Leandrodn/Project5-6-RDM-RegistatiePaal/Onderzoek/Gebruikers_Onderzoek/Enquete_Document.pdf

# Enquête

# Werkplaatsregistratie

Wie: 2e Jaars Technische Informatica studenten

Waarom: Uitzoeken wat studenten het fijnste registratiesysteem vinden

Doel: Automatiseren van registratie studenten die de werkplaatsen gebruiken

Waarvoor: Project – Help de RDM werkplaatsen met studentenregistratie

# Graag Scannen en Invullen

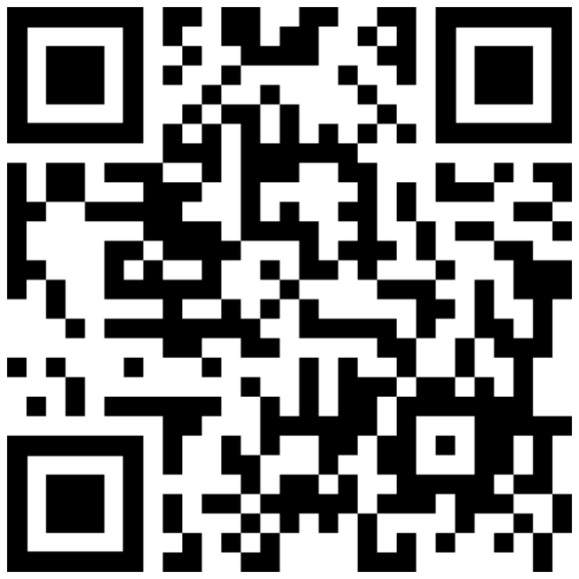
[picture p20: figure]
