Leandrodn/Project5-6-RDM-RegistatiePaal/Onderzoek/Gebruikers_Onderzoek/Onderzoek_Registratiemethodes.pdf

# Onderzoek Registratiemethodes – Project

56

Help de RDM-werkplaatsen om beter grip te krijgen op het gebruik van de werkplaatsen!


Projectleden:
- Matthijs Briel (0988991)
- Leandro de Nijs (1003440)
- Tom van Pelt (1003212)
- Gijs Kortlever (1003152)
Inleverdatum: 6 Februari 2022
Begeleiders: Erwin de Mos & S.M. Hekkelman Bedrijfsbegeleider (Product Owner): F.W.J. Joosten Gladon Gelegenheid: Eerste Kans


# Inhoudsopgave

# Inleiding

In dit document wordt er onderzocht wat de beste registratiemethode is voor het gebruik maken van de werkplaatsen. Hiervoor wordt er een enquête gedaan onder de studenten die gebruik maken van de werkplaatsen en worden er interviews gedaan met een aantal instructeurs om een beeld te krijgen wat zij voor ogen hebben en of zij nog speciale wensen / eisen hebben voor hun werkplaats.

De mensen die gebruik gaan maken van ons registratiesysteem zijn de studenten die een werkplaats willen gebruiken. De instructeurs worden hierdoor ondersteund door een taak van hun erg te verlichten (het handmatig registreren van studenten).

# Enquête Onder Studenten

Onder de studenten wordt er dus een enquête gehouden. Via een enquête kunnen we heel makkelijk een grootte doelgroep bereiken. De minimale hoeveelheid studenten die aan onze enquête moet deelnemen valt te bepalen met een berekening. Om dit te berekenen hebben we een aantal initiële waardes nodig.

- De populatie: dit is aan hoeveel mensen de enquête wordt voorgelegd. Dit hangt ook af van hoelang we de data willen ontvangen, we laten de enquête een week hangen in de drie meest gebruikte werkplaatsen, de houtwerkplaats, metaalwerkplaats en het Protolab. Ook zullen er een of meerdere dagen actief mensen werven voor deelname. Om onze populatie dus te bepalen moeten we weten hoeveel mensen er in een week tijd naar de werkplaatsen gaan, dit kunnen we halen uit de data van 2019 die we hebben gekregen van ons product owner. Gemiddeld komen er 172 studenten per week naar de werkplaatsen, dit verdelen over 8 werkplaatsen is 21 studenten per week per werkplaats. De enquête wordt gehouden bij drie werkplaatsen, dus 21 x 3 = 63 studenten.
- Foutmarge: die is hoe zeker wij ervan zijn dat de mening van de ondervraagde overeenkomt met die van de totale populatie. Voor enquêtes wordt vaak een foutmarge genomen van 5%, er zal hier ook mee werken.
- Betrouwbaarheidsinterval: dit is hoe zeker wij zijn dat het resultaat een nauwkeurige afspiegeling van de populatie vormt. Voor enquêtes wordt vaak het 95% betrouwbaarheid interval gebruikt, er zal hier ook mee gerekend worden.
- Als we dit berekenen via een formule of via een online calculator, komen we erachter dat we minimaal 55 respondenten moeten verkrijgen voor een betrouwbaar resultaat. Zie Figuur 1.

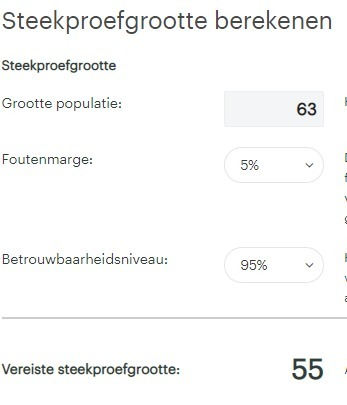
[picture p21: figure]

Figuur 1 - Steekproefgrootte Berekening

1

1 Steekproefomvang berekening: https://nl.checkmarket.com/steekproefcalculator/

### Link naar enquête

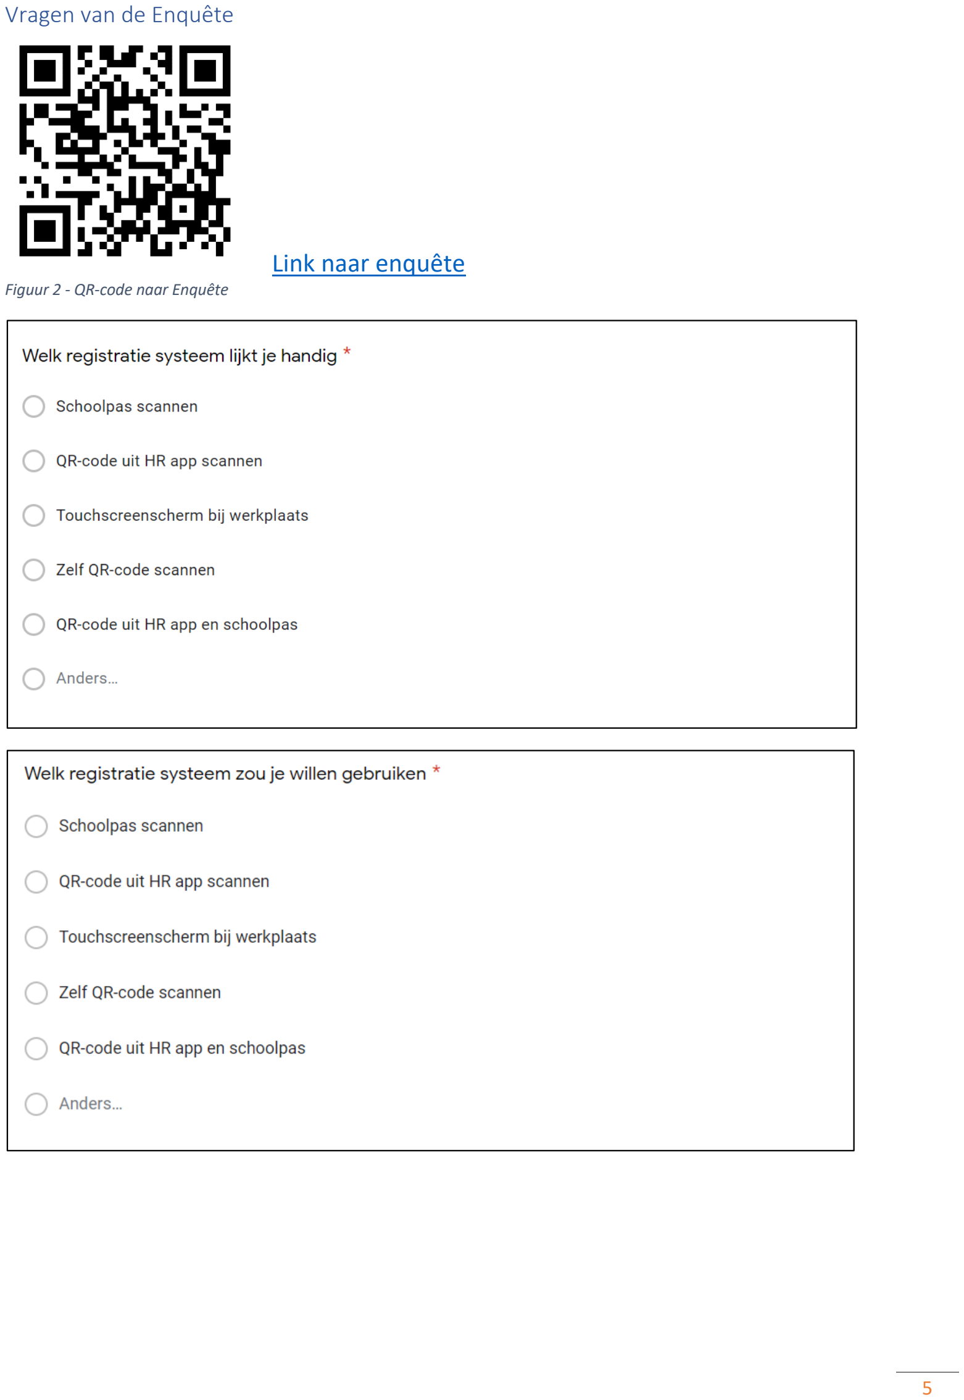
[picture p22: page 5]

### Vragen van de Enquête

Figuur 2 - QR-code naar Enquête

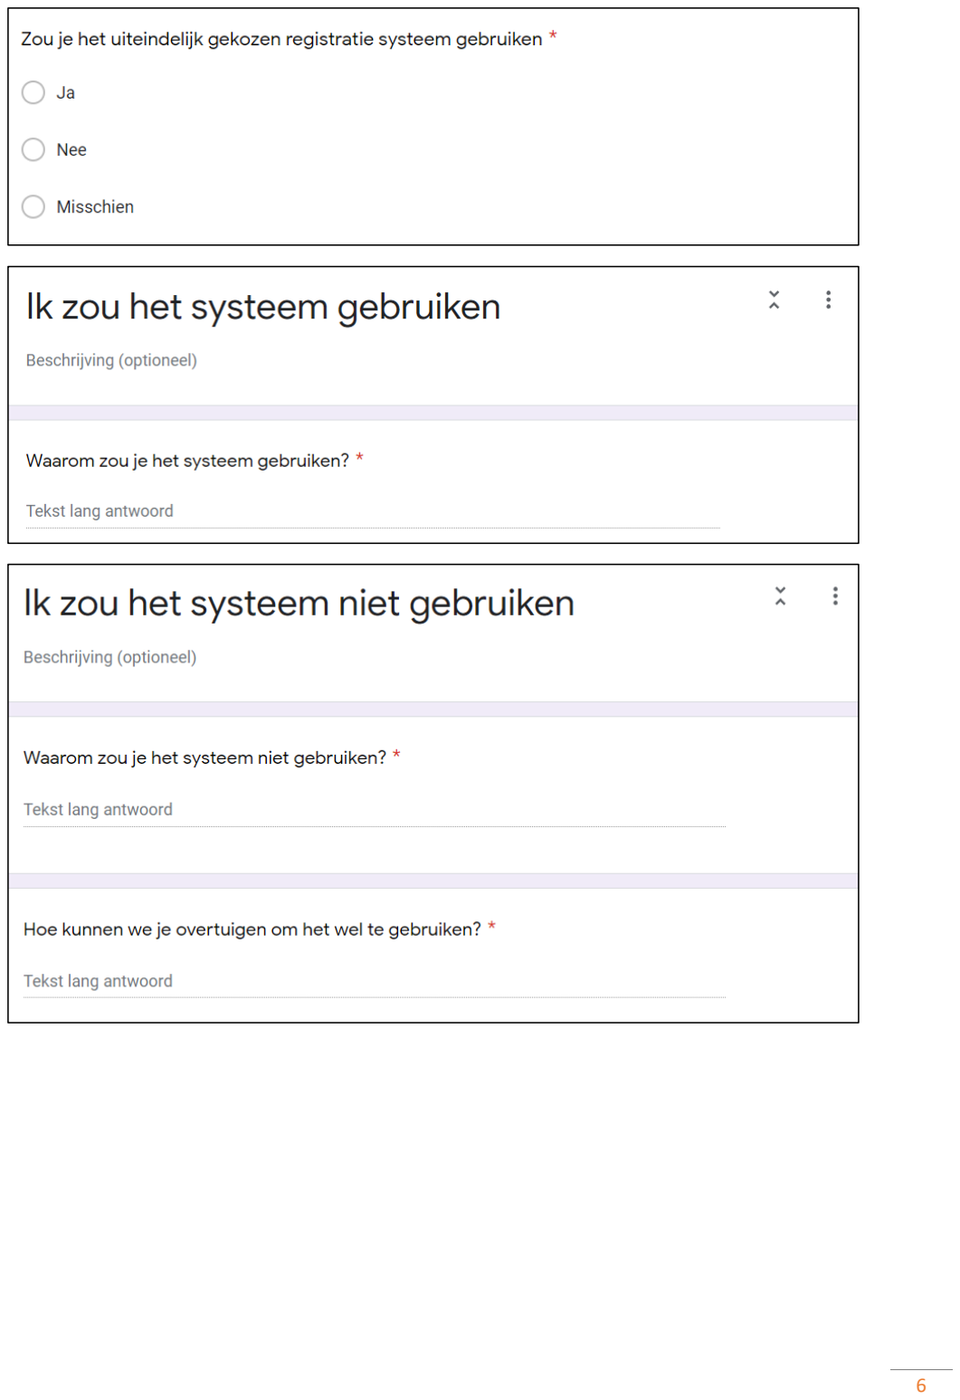
[picture p23: page 6]
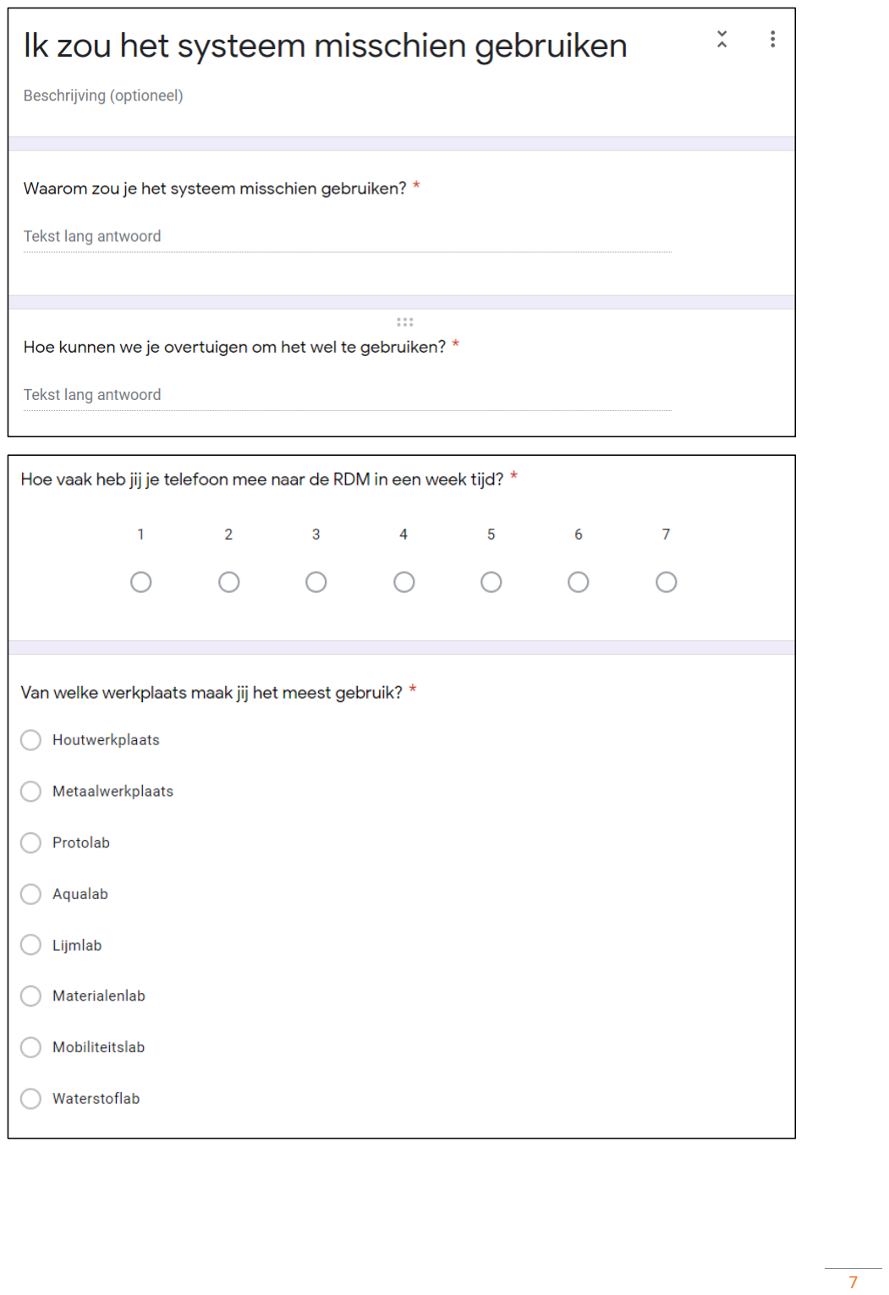
[picture p24: page 7]

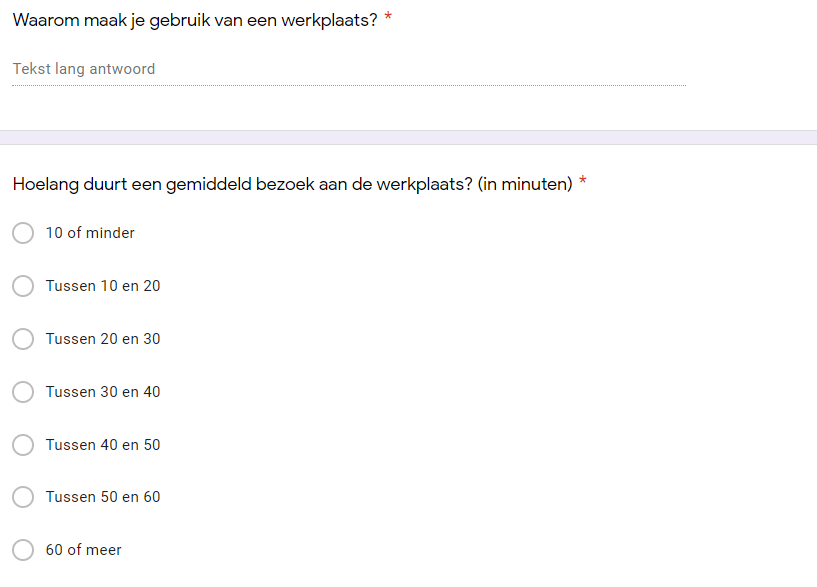
[picture p25: figure]
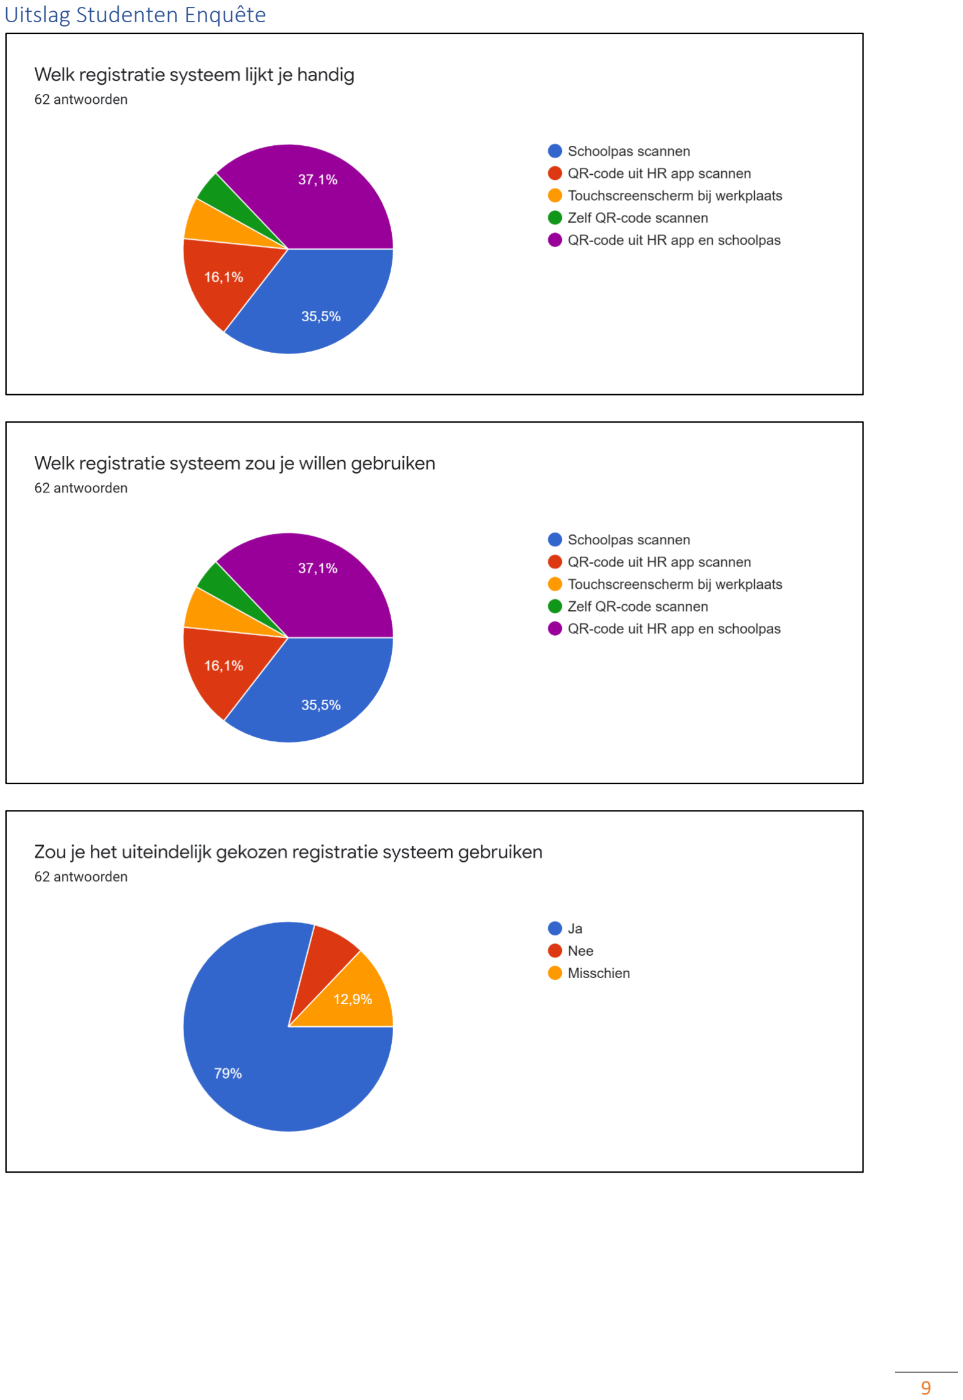
[picture p26: page 9]

### Uitslag Studenten Enquête

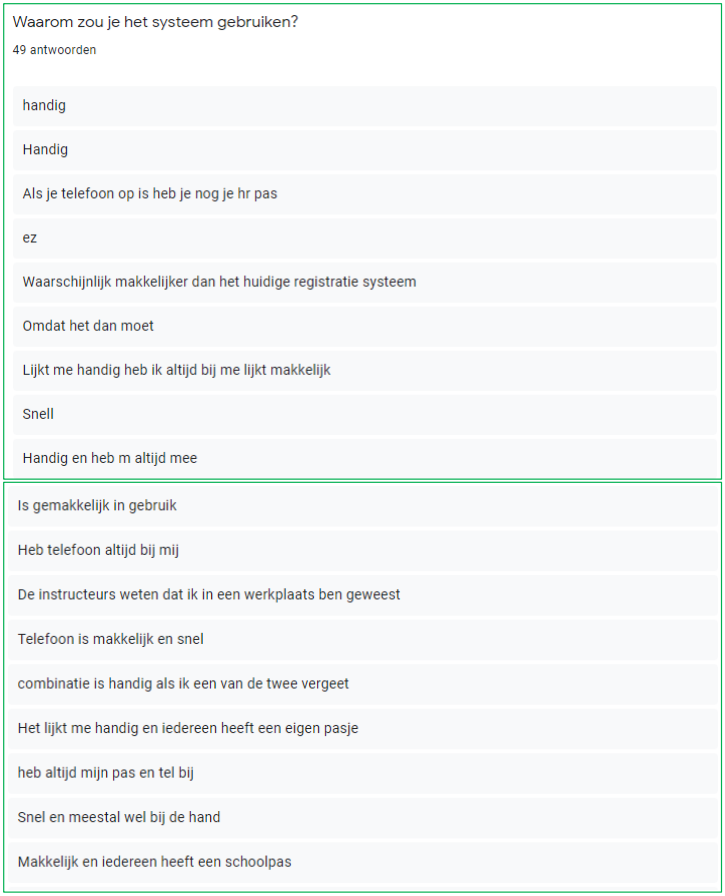
[picture p27: figure]

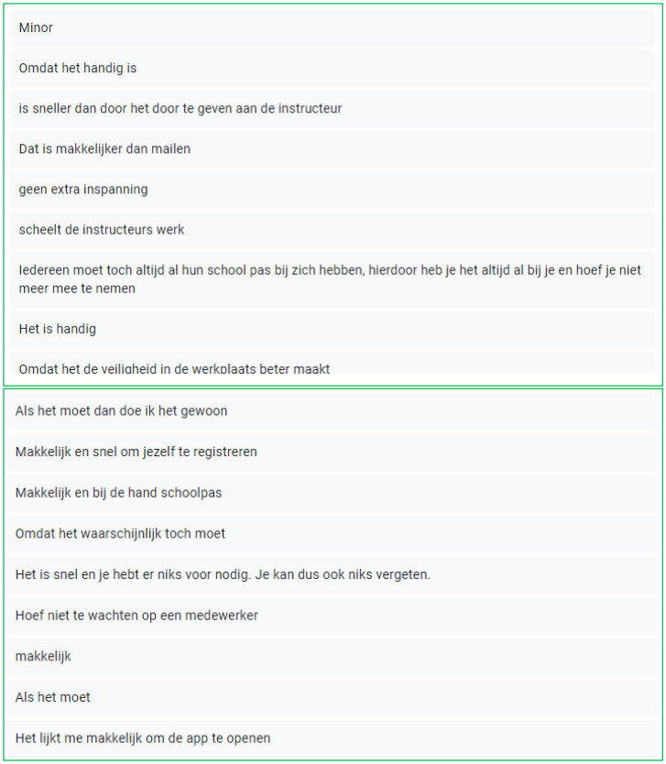
[picture p28: figure]

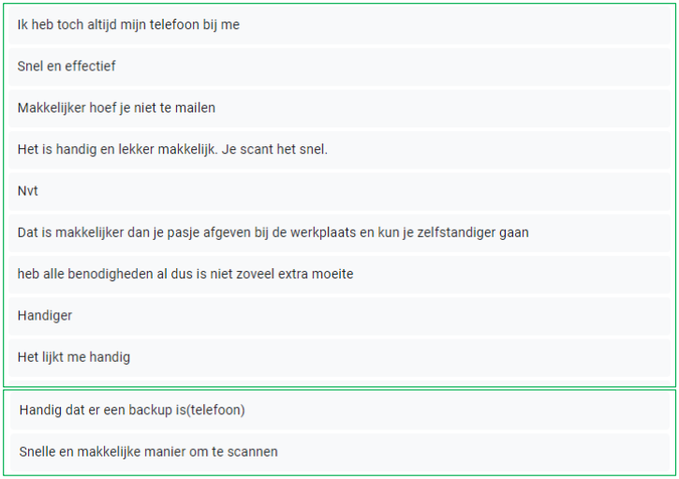
[picture p29: figure]
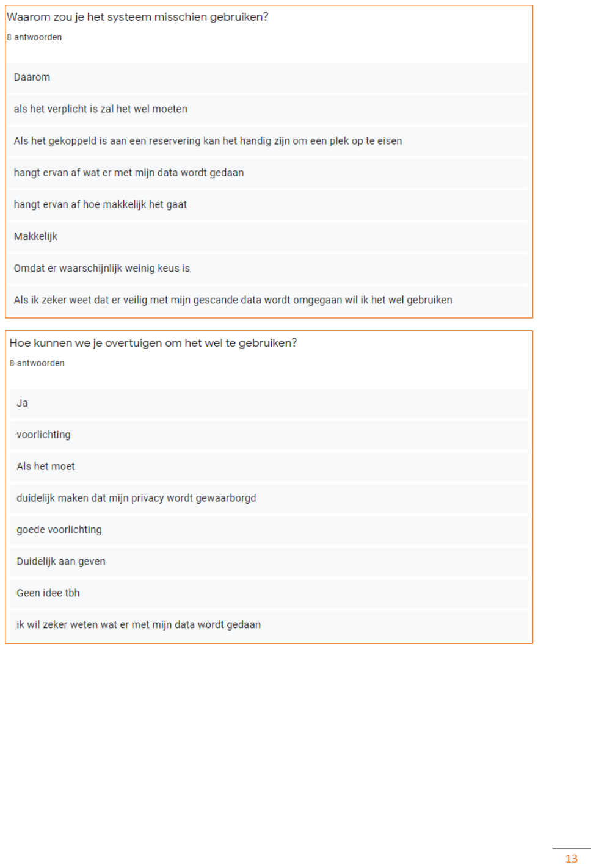
[picture p30: page 13]
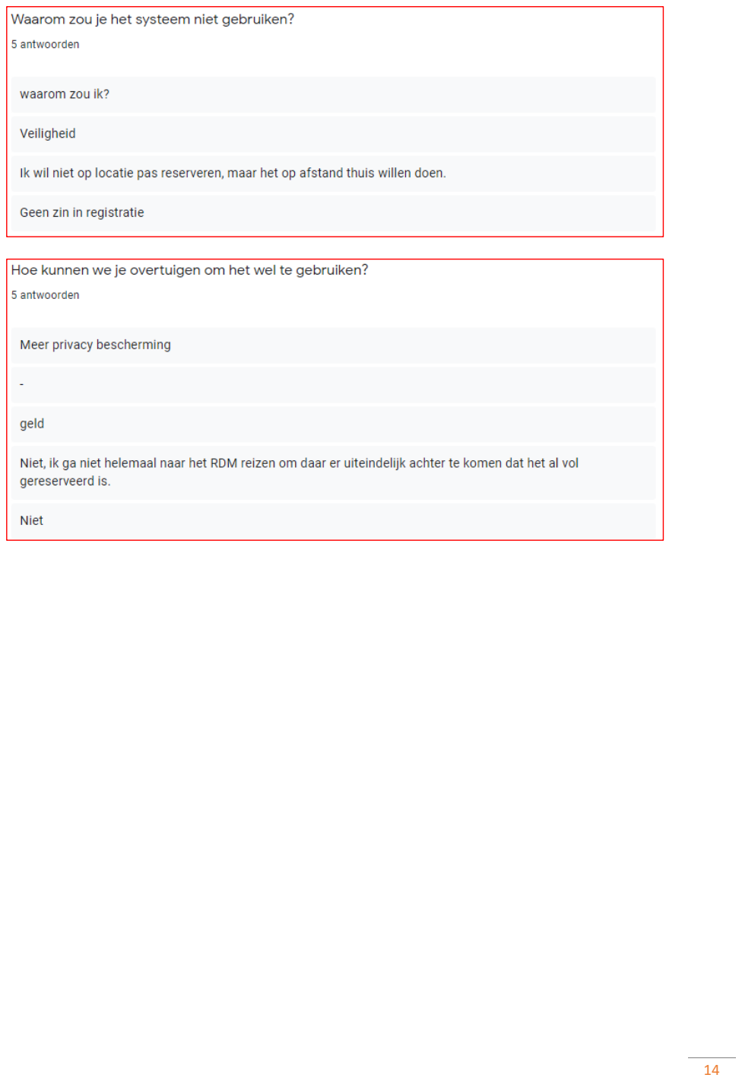
[picture p31: page 14]
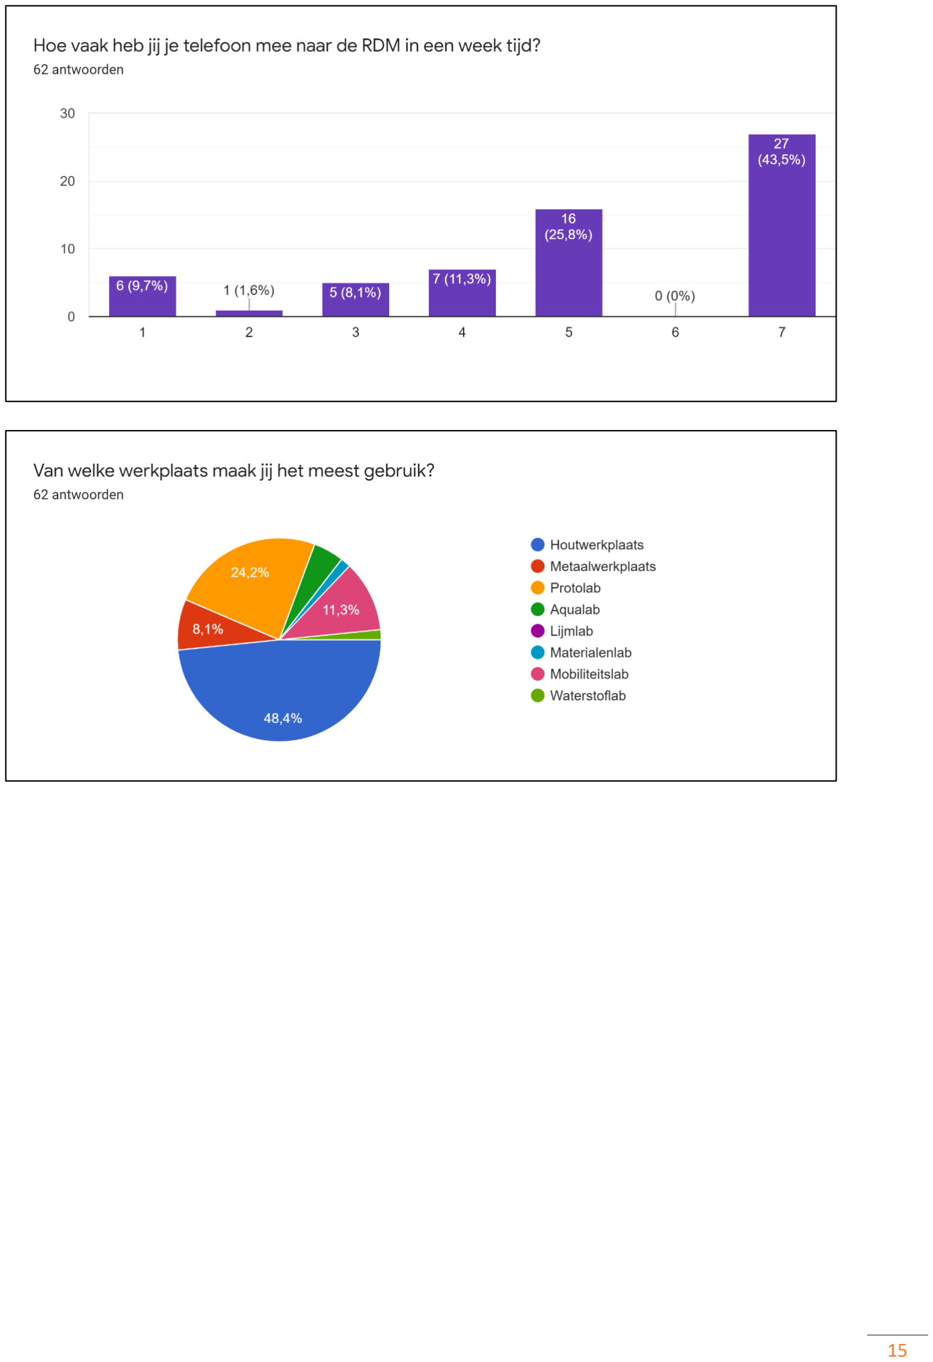
[picture p32: page 15]

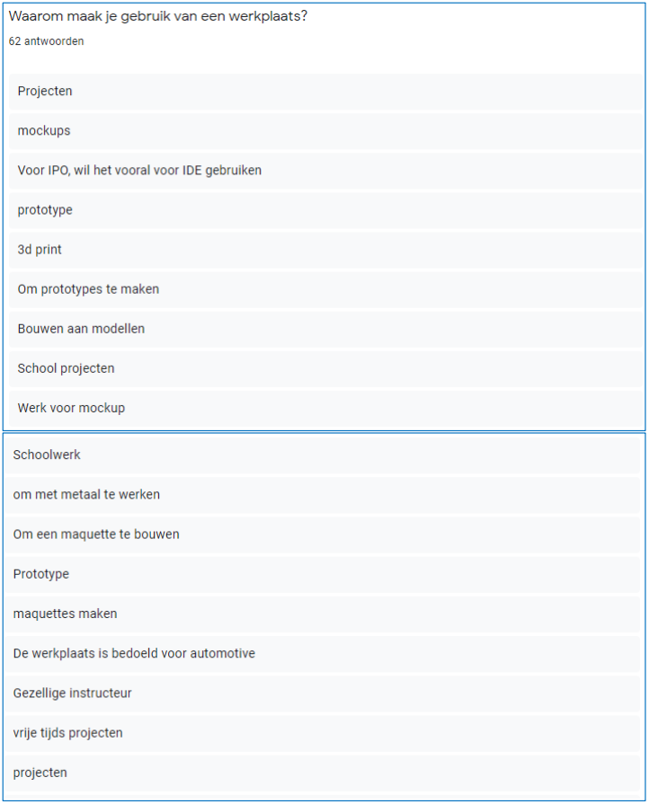
[picture p33: figure]

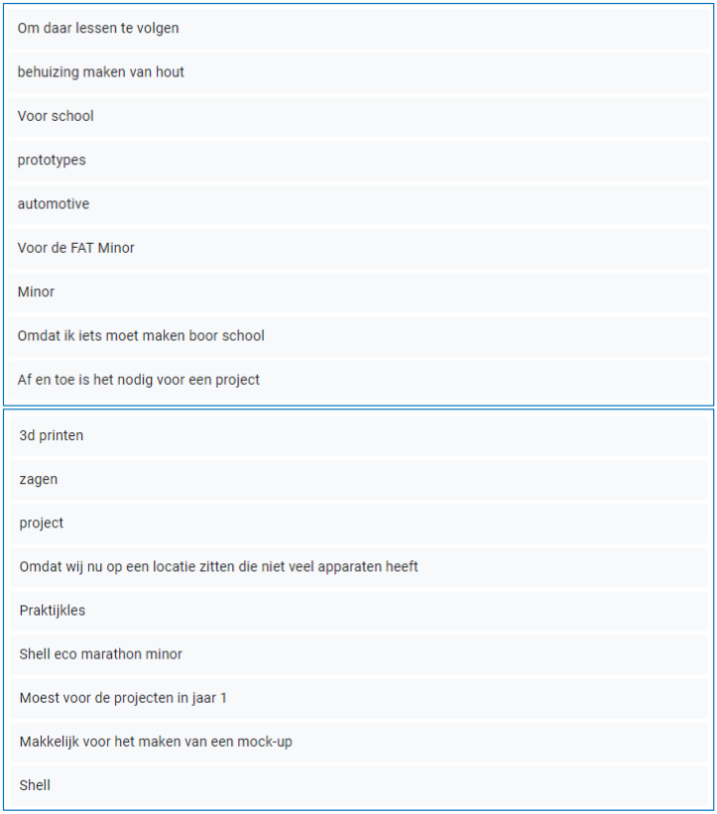
[picture p34: figure]

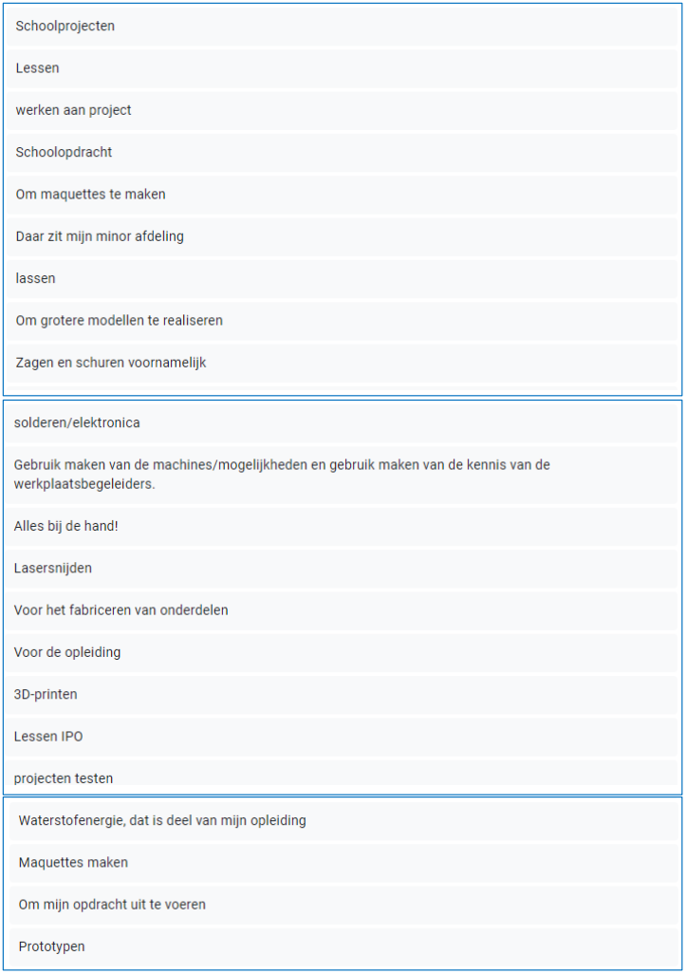
[picture p35: figure]

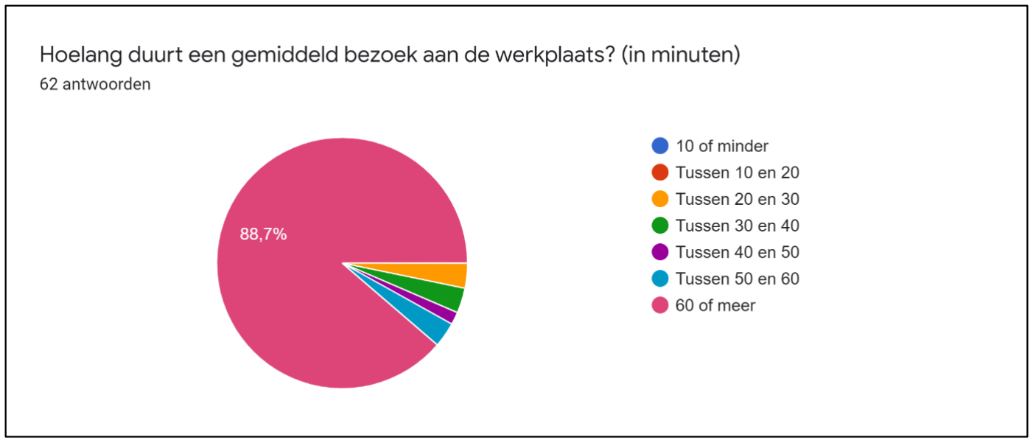
[picture p36: figure]

### Resultaten Enquête

- Het registratiesysteem dat de studenten het handigste lijkt is de QR-Code uit de HR App en de Barcode op de HR-pas.
- De studenten die bovenstaande codes het handigste lijkt om te gebruiken zouden deze ook echt gaan gebruiken.
- Omdat bijna 90% de barcode op de HR-pas, QR-Code uit de HR App of beide het handigste lijkt en zou willen gebruiken, willen bijna 80% van de studenten ook het registratiesysteem uiteindelijk gaan gebruiken en bijna 13% misschien.
- De belangrijkste redenen waarom mensen het systeem willen gebruiken zijn: handig, ik heb altijd mijn schoolpas bij mij, ik heb altijd mijn telefoon bij mij en handiger dan het huidige systeem.
- De belangrijkste redenen waarom mensen het systeem misschien willen gebruiken zijn: er is waarschijnlijk weinig keus, hangt af van hoe makkelijk het systeem werkt en ik wil zeker weten dat mijn data veilig blijft.
- Om het wel te gebruiken willen de studenten graag: goede voorlichting en zeker weten dat mijn data veilig blijft.
- De belangrijkste redenen waarom mensen het systeem niet willen gebruiken zijn: waarom zou ik, geen zin om mij te registreren en veiligheid.
- Om het wel te gebruiken willen de studenten graag: meer privacybescherming, geld en een aantal willen het helemaal niet.
- Bijna iedereen heeft zijn telefoon eigenlijk altijd mee naar de RDM.
- De werkplaats die het meest gebruikt wordt is de houtwerkplaats met bijna 50%. Daarna komt het Protolab en daarna het Mobiliteitslab.
- De belangrijkste redenen waarom mensen gebruik maken van een werkplaats zijn:
- Houtwerkplaats: voor mockup(s), minor, maquettes en om grote modellen te maken.
- Protolab: prototypes maken, schoolprojecten, Shell ECO Marathon en voor andere schoolopdrachten.
- Mobiliteitslab: schoolopdrachten en voor lessen.
- Een gemiddeld bezoek aan een werkplaats duurt in bijna 90% van de gevallen langer dan 60 minuten.

### Conclusie

- De conclusie de getrokken kan worden is dat er een registratiesysteem gemaakt moet worden die een barcode op HR-pas en QR-Code uit de HR-app kan scannen. De meeste studenten vinden dit een handige registratiemethode en willen dit uiteindelijk ook gebruiken. Om de studenten over te halen die het systeem misschien of niet willen gebruiken moet het systeem goed beveiligd worden, voldoen aan de AVG-regels, er moet goede voorlichting komen welke data wordt geregistreerd en wat hiermee gedaan wordt en hoe het registratiesysteem gebruikt moet worden.

# Interviews Instructeurs

Er zijn bij de instructeurs van verschillende werkplaatsen interviews afgenomen om een beeld te krijgen van het product dat zij voor ogen hebben. Er zijn interviews afgenomen van de instructeur van de Metaalwerkplaats, Houtwerkplaats, Protolab en Aqualab.

### Vragen

Voor dit interview zijn een aantal vragen opgesteld:
1. Wat zijn problemen waar u nu tegen aan loopt via het huidige systeem?
2. Wie hebben er allemaal toegang tot de werkplaatsen?
3. Wordt er veel gereserveerd of is er veel vrije inloop?
4. Hoe kunnen wij het registreren voor u makkelijker maken?
5. Met welke dingen moeten we rekening houden in uw werkplaats?
6. Wat doen jullie met mensen die alleen iets willen pakken of even naar binnen gaan (wel of niet registreren)?
7. Hoeveel in- en uitgangen zijn er in deze werkplaats?
8. Wanneer zijn jullie aanwezig?

De antwoorden op deze vragen waren bij alle werkplaatsen samengevat zo:
1. Nu moeten alle bezoeken van studenten aan de werkplaatsen met de hand worden geregistreerd door het op te schrijven of in een Excel bestand te zetten. Ook moet een eventuele afsprakenlijst met de hand worden afgevinkt. Deze werkzaamheden kosten de instructeurs veel onnodige tijd.
2. De mensen die toegang hebben tot de werkplaatsen zijn de studenten (op afspraak of na vragen aan instructeurs), instructeurs zelf en bepaalde bevoegde medewerkers (zijn er niet veel).
3. Bij de Houtwerkplaats en Protolab is er vooral veel vrije inloop. Bij de andere werkplaatsen is het bijna alleen maar op afspraak.
4. Wij kunnen het registreren makkelijker maken door een systeem te bedenken waar studenten zich kunnen registreren zonder dat de instructeur daar veel extra werk aan heeft. De registraties moeten inzichtelijk zijn voor de instructeurs en administratieve medewerkers.
5. Bij bepaalde werkplaatsen moet rekening worden gehouden met de plaatsing van een eventuele registratiepaal, omdat daar bijvoorbeeld geen of slecht internet is of geen stroom aansluiting. Bij het Aqualab zou de instructeur het eventuele registratieapparaat aan het hek willen hangen in plaats van op een paal.
6. De meeste instructeurs registreren studenten die even iets willen pakken of iets willen vragen niet.
7. Zie het document: Inventarisatie Werkplaatsen.
8. Zie het document: Inventarisatie Werkplaatsen.

### Wensen & Tips

Een samenvatting van de antwoorden als wensen en tips van de instructeurs:
- Instructeurs hebben baat bij een centrale registratie.
- De administratie wordt duidelijker met een scan registratiesysteem, doordat iedere student die gebruik wil maken van een werkplaats zich moet registreren bij een scan systeem. De instructeur hoeft dit niet meer te doen en kan dit dus ook niet meer vergeten.
- Wel moet de vrije inloop behouden blijven. Dus geen systeem met bijv. poortjes voor binnenkomst.
- Wel moet er gekeken worden naar de kwetsbaarheid van een systeem wat er wordt ontwikkeld.
- Het gebruik maken van de werkplaatsen wordt alleen gezien als de studenten echt iets maken of testen in de werkplaats. Niet als de studenten alleen iets willen vragen of lenen.

### Conclusie

- Er moet vrije inloop blijven, de instructeurs willen niet dat studenten worden gehinderd bij binnenkomst van een werkplaats. Ook moet het product gaan zorgen voor een duidelijke administratie voor de instructeurs. Een belangrijke tip die werd gegeven door de instructeurs was om de kwetsbaarheden goed te onderzoeken en te verhelpen.
- Al met al, de instructeurs zullen blij zijn als er een registratiesysteem komt waaraan zij bijna tot geen werk hebben.

# Changelog

Versie | Datum | Aanpassing | Auteur
1.0 | 05/11/2021 | Eerste versie | Leandro de Nijs
1.1 | 13/11/2021 | Extra koppen toegevoegd en foto’s van enquête ingevoegd | Leandro de Nijs
1.2 | 19/11/2021 | Lay-out aanpassingen | Tom van Pelt
1.3 | 20/11/2021 | Link en QR-code naar enquête toegevoegd | Tom van Pelt
1.4 | 26/11/2021 | Voorlopige uitslag van studenten enquête toegevoegd. Uitslag Interviews met instructeurs toegevoegd | Tom van Pelt & Gijs Kortlever
1.5 | 15/01/2022 | Afbeeldingen op Voorblad toegevoegd | Tom van Pelt
1.6 | 19/01/2022 | Lay-out aangepast, changelog toegevoegd, info toegevoegd | Tom van Pelt & Leandro de Nijs
1.7 | 20/01/2022 | Verslag verder veel aangevuld, uiteindelijke uitslag enquête erin gezet en interviews met instructeurs toegevoegd, algemener omgezet | Tom van Pelt & Leandro de Nijs
