Leandrodn/Project5-6-RDM-RegistatiePaal/Ontwerpen_en_Schema's/Architectuur_Ontwerp/Architectuur_ontwerp_huidig.png

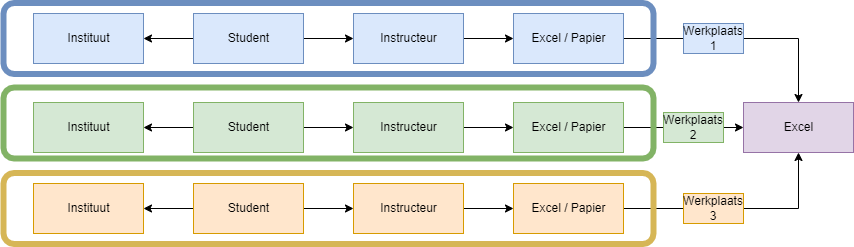
Ontwerpen_en_Schema's/Architectuur_Ontwerp/Architectuur_ontwerp_huidig.png
