Leandrodn/Project5-6-RDM-RegistatiePaal/Ontwerpen_en_Schema's/Attack_Trees/Attack_Tree_P56.png

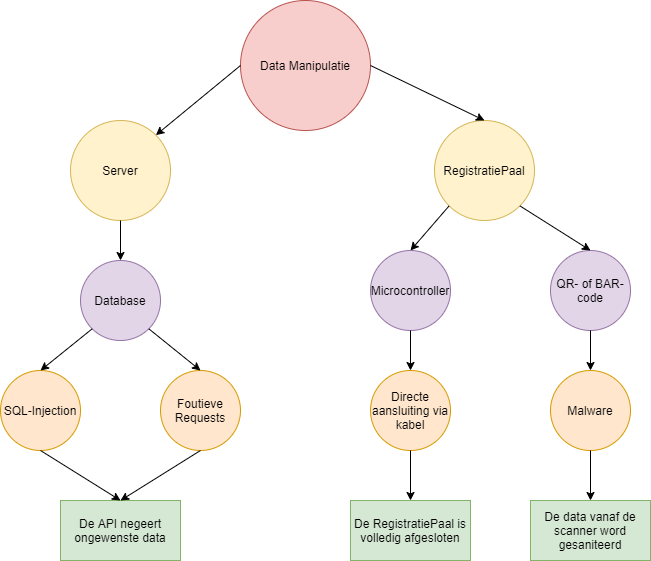
Ontwerpen_en_Schema's/Attack_Trees/Attack_Tree_P56.png
