Leandrodn/Project5-6-RDM-RegistatiePaal/Ontwerpen_en_Schema's/Attack_Trees/Attack_Tree_P56V2.png

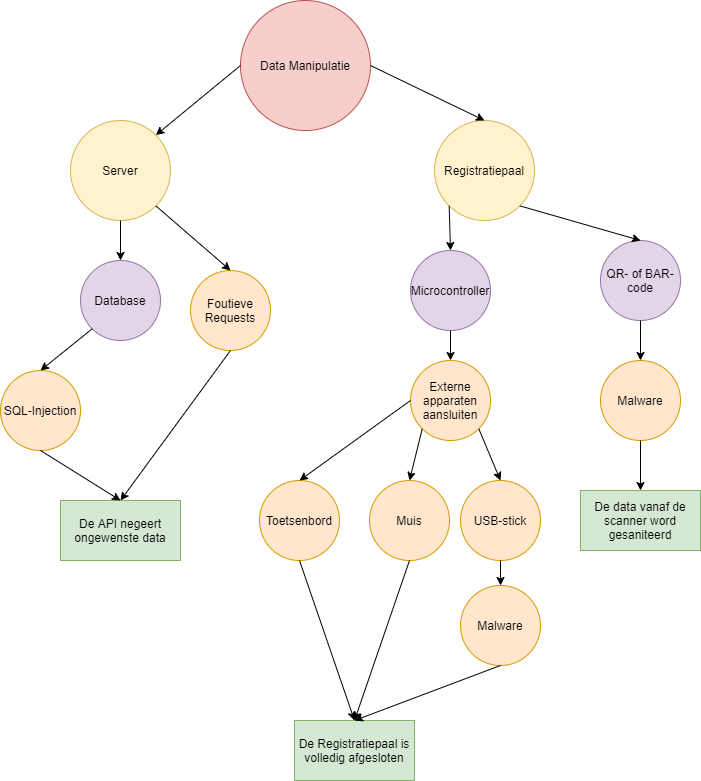
Ontwerpen_en_Schema's/Attack_Trees/Attack_Tree_P56V2.png
