Leandrodn/Project5-6-RDM-RegistatiePaal/Ontwerpen_en_Schema's/ERD/ERD/ERD_Database_Project56_V5.png

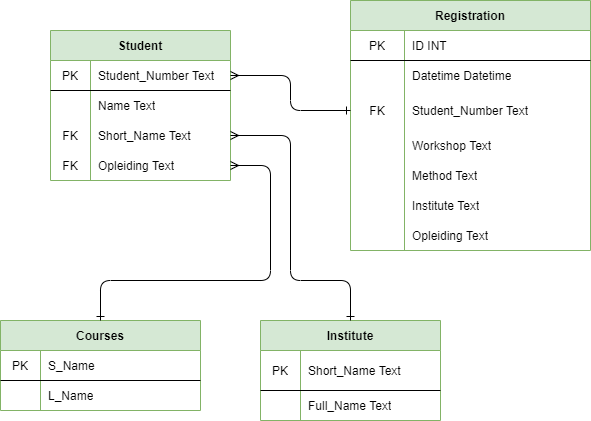
Ontwerpen_en_Schema's/ERD/ERD/ERD_Database_Project56_V5.png
