Leandrodn/Project5-6-RDM-RegistatiePaal/Ontwerpen_en_Schema's/GUI_Schermen/HTTP_400_Errorscreen-GUI.png

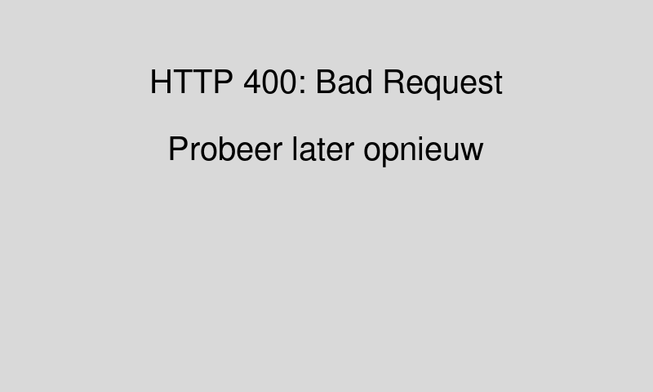
Ontwerpen_en_Schema's/GUI_Schermen/HTTP_400_Errorscreen-GUI.png
