Leandrodn/Project5-6-RDM-RegistatiePaal/Ontwerpen_en_Schema's/GUI_Schermen/No_Connection_Errorscreen-GUI.png

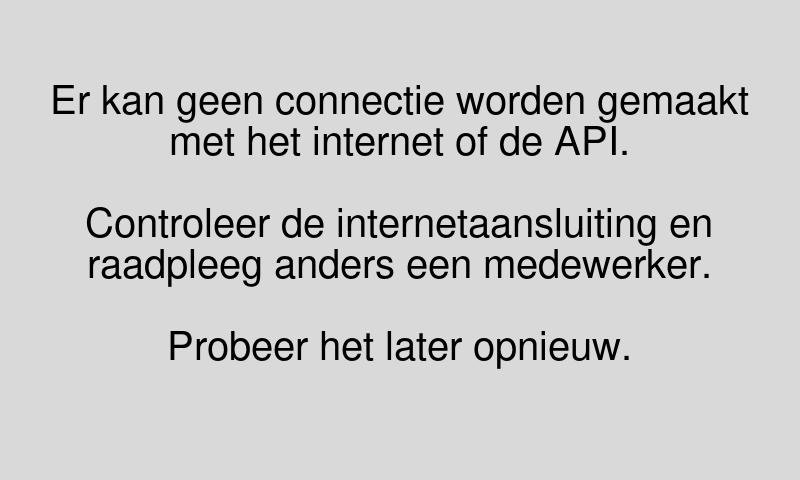
Ontwerpen_en_Schema's/GUI_Schermen/No_Connection_Errorscreen-GUI.png
