Leandrodn/Project5-6-RDM-RegistatiePaal/Ontwerpen_en_Schema's/GUI_Schermen/Success_Screen-GUI.png

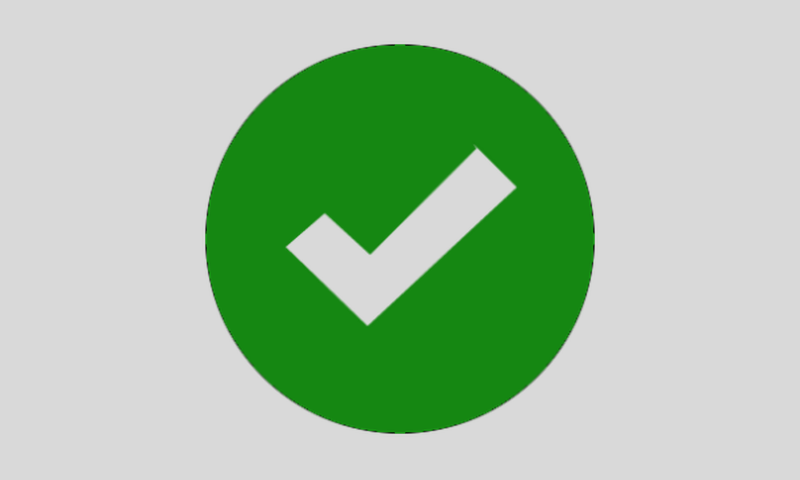
Ontwerpen_en_Schema's/GUI_Schermen/Success_Screen-GUI.png
