Leandrodn/Project5-6-RDM-RegistatiePaal/How_To_Build_Your_Own_Registratiesysteem/Detail_Foto's/5FF52AF8-A50F-4575-A561-C6657E2B4982.jpeg

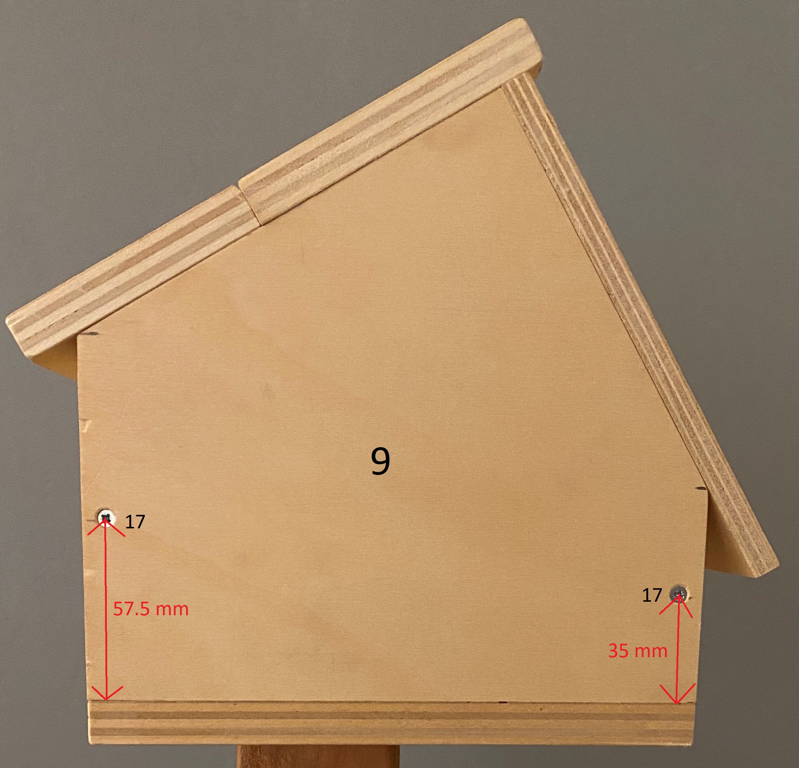
How_To_Build_Your_Own_Registratiesysteem/Detail_Foto's/5FF52AF8-A50F-4575-A561-C6657E2B4982.jpeg
