Leandrodn/Project5-6-RDM-RegistatiePaal/How_To_Build_Your_Own_Registratiesysteem/Detail_Foto's/6F3235FF-34C5-47BE-BF38-D8AC5AD66240.jpeg

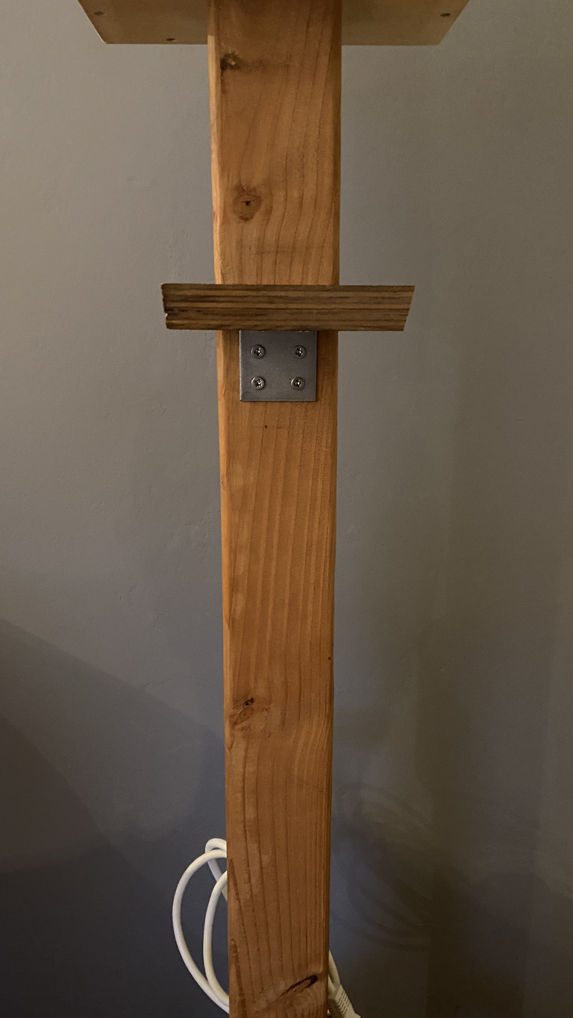
How_To_Build_Your_Own_Registratiesysteem/Detail_Foto's/6F3235FF-34C5-47BE-BF38-D8AC5AD66240.jpeg
