Leandrodn/Project5-6-RDM-RegistatiePaal/How_To_Build_Your_Own_Registratiesysteem/Detail_Foto's/945FF0A9-7452-492A-9D4D-75E6C9FA574E.jpeg

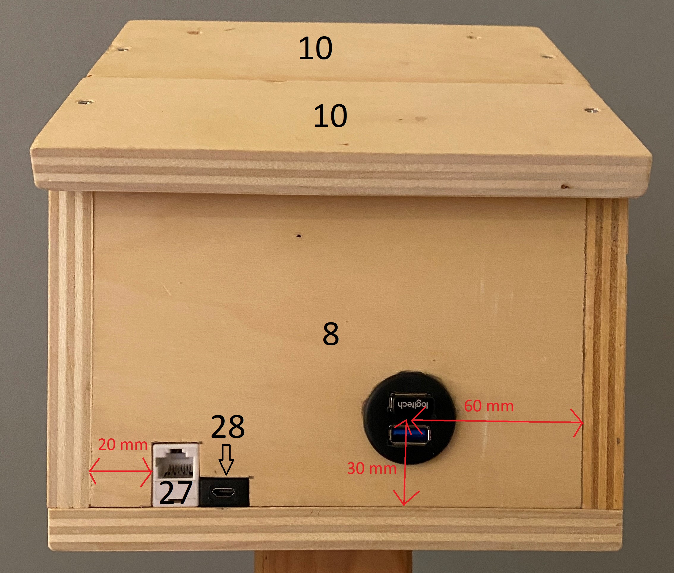
How_To_Build_Your_Own_Registratiesysteem/Detail_Foto's/945FF0A9-7452-492A-9D4D-75E6C9FA574E.jpeg
