Leandrodn/Project5-6-RDM-RegistatiePaal/How_To_Build_Your_Own_Registratiesysteem/Detail_Foto's/91525563-372B-43A3-8AC4-569709F1212C.jpeg

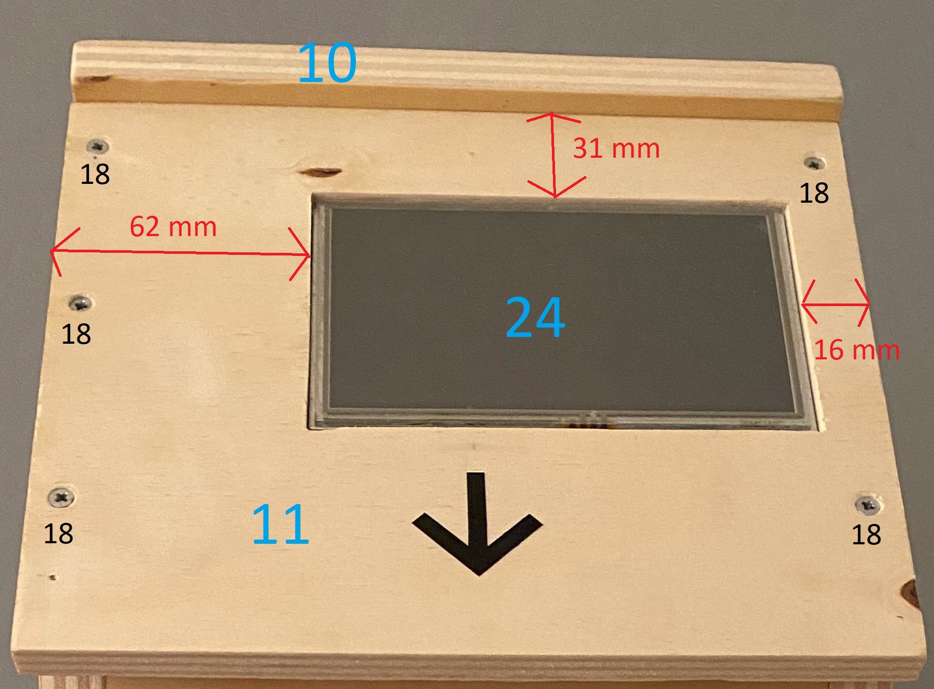
How_To_Build_Your_Own_Registratiesysteem/Detail_Foto's/91525563-372B-43A3-8AC4-569709F1212C.jpeg
