Leandrodn/Project5-6-RDM-RegistatiePaal/How_To_Build_Your_Own_Registratiesysteem/Detail_Foto's/ABB2F962-6038-484A-A4DD-B39C9B3D00F8.jpeg

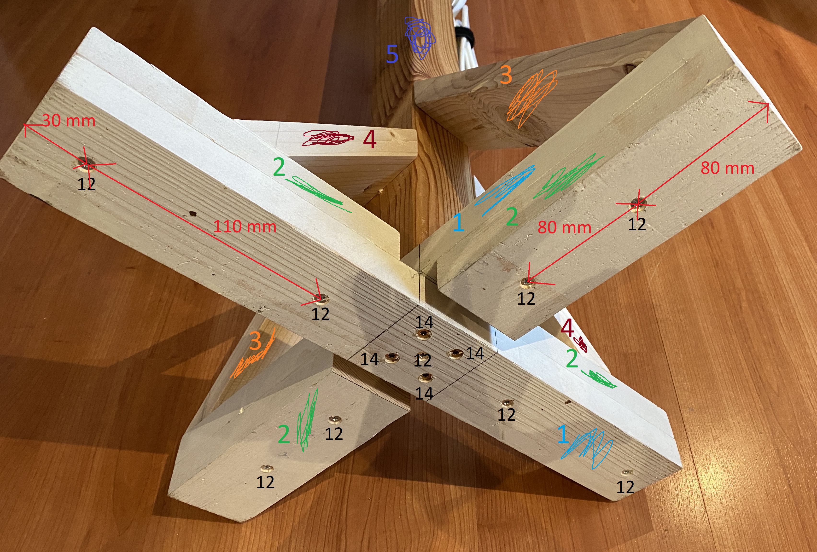
How_To_Build_Your_Own_Registratiesysteem/Detail_Foto's/ABB2F962-6038-484A-A4DD-B39C9B3D00F8.jpeg
