Leandrodn/Project5-6-RDM-RegistatiePaal/How_To_Build_Your_Own_Registratiesysteem/Detail_Foto's/C11E28FF-22F5-4392-A392-7CBB54A06A5C.jpeg

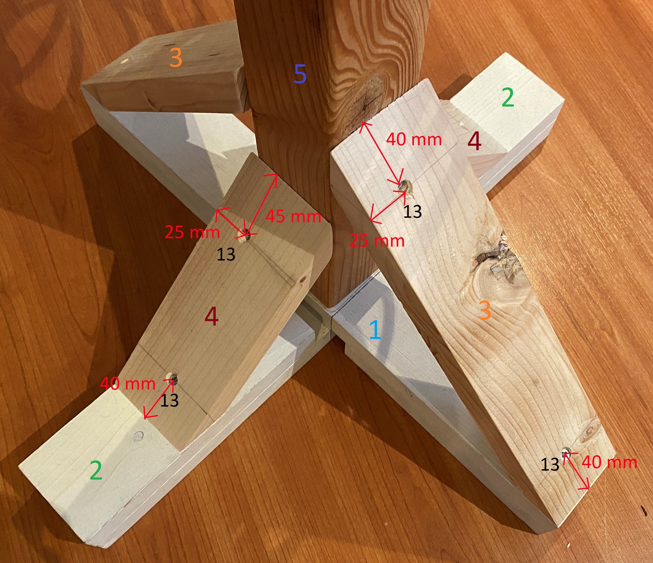
How_To_Build_Your_Own_Registratiesysteem/Detail_Foto's/C11E28FF-22F5-4392-A392-7CBB54A06A5C.jpeg
