Leandrodn/Project5-6-RDM-RegistatiePaal/How_To_Build_Your_Own_Registratiesysteem/Detail_Foto's/C12F5491-6F91-4C54-9CF0-839FC8C42175.jpeg

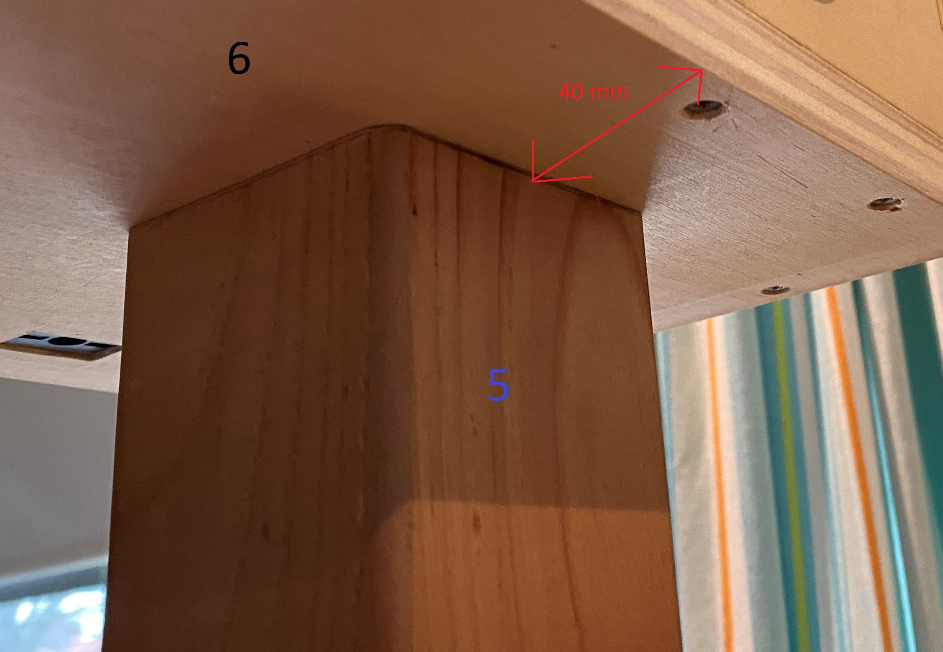
How_To_Build_Your_Own_Registratiesysteem/Detail_Foto's/C12F5491-6F91-4C54-9CF0-839FC8C42175.jpeg
