Leandrodn/Project5-6-RDM-RegistatiePaal/How_To_Build_Your_Own_Registratiesysteem/Detail_Foto's/C8036F05-C584-4316-8C60-5978D1E8C08D.jpeg

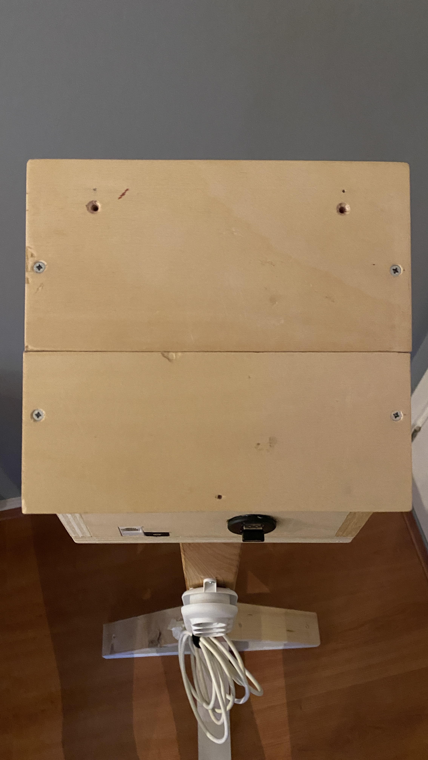
How_To_Build_Your_Own_Registratiesysteem/Detail_Foto's/C8036F05-C584-4316-8C60-5978D1E8C08D.jpeg
