Leandrodn/Project5-6-RDM-RegistatiePaal/Ontwerpen_en_Schema's/Elektrisch_Schema/Elektrisch_Schema_Registratie_Paal.pdf

# GNDMicro USB

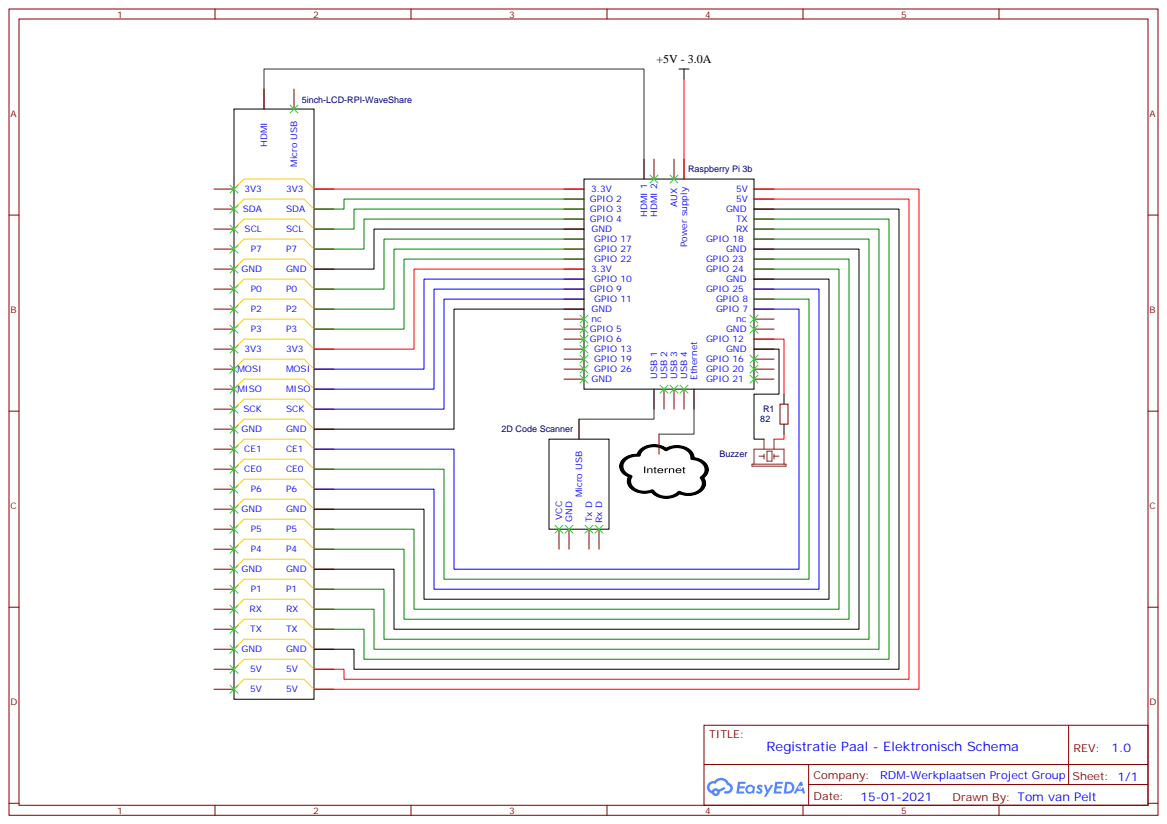
[picture p72: page 1]

Company: RDM-Werkplaatsen Project Group

Drawn By: Tom van Pelt
