Leandrodn/Project5-6-RDM-RegistatiePaal/Ontwerpen_en_Schema's/3D-Ontwerp/RegistratiePaal-3D.pdf

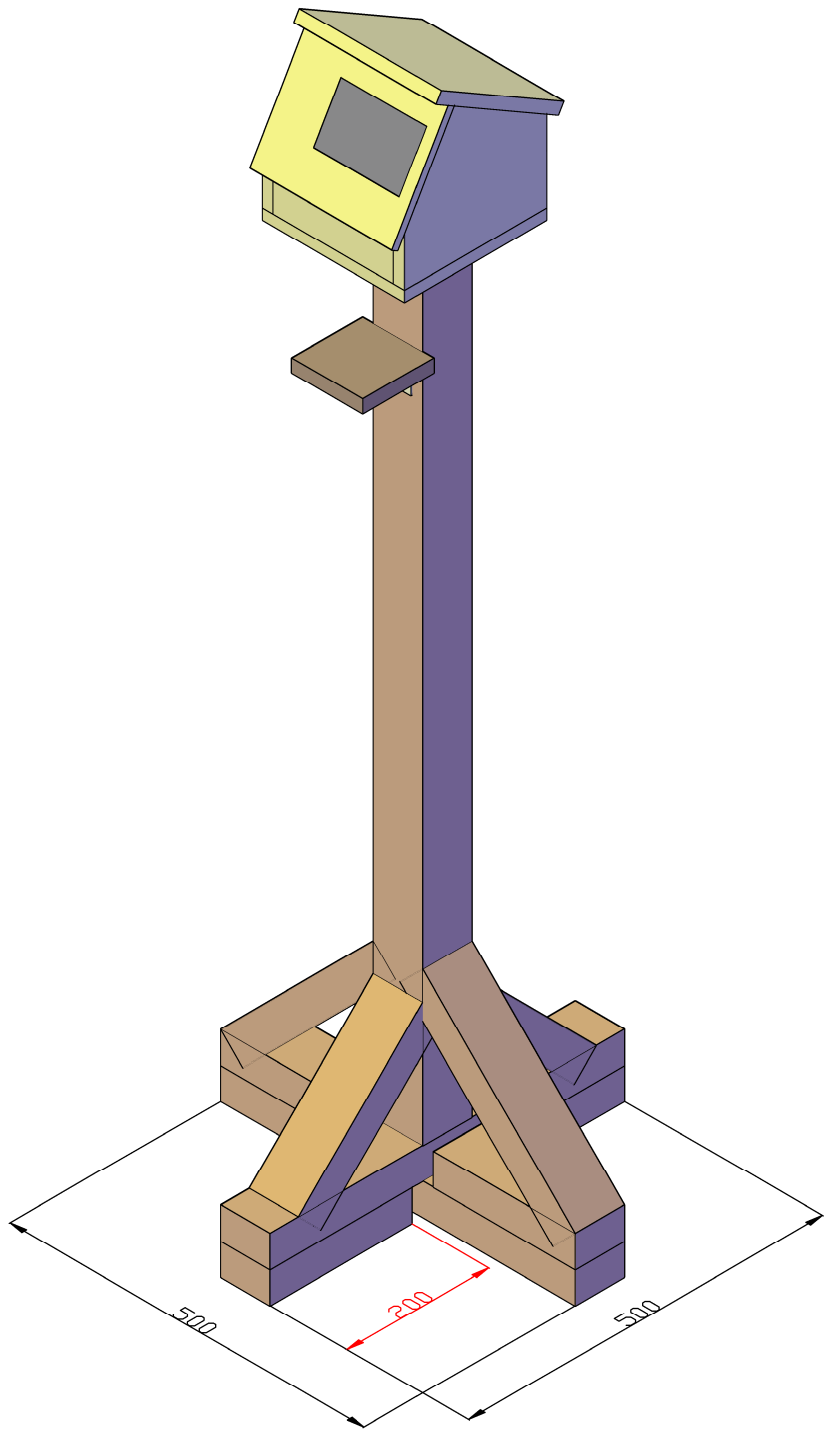
[picture p73: page 1]
