Leandrodn/Project5-6-RDM-RegistatiePaal/Ontwerpen_en_Schema's/3D-Ontwerpen_Afmetingen/Achteraanzicht-Registratiepaal.pdf

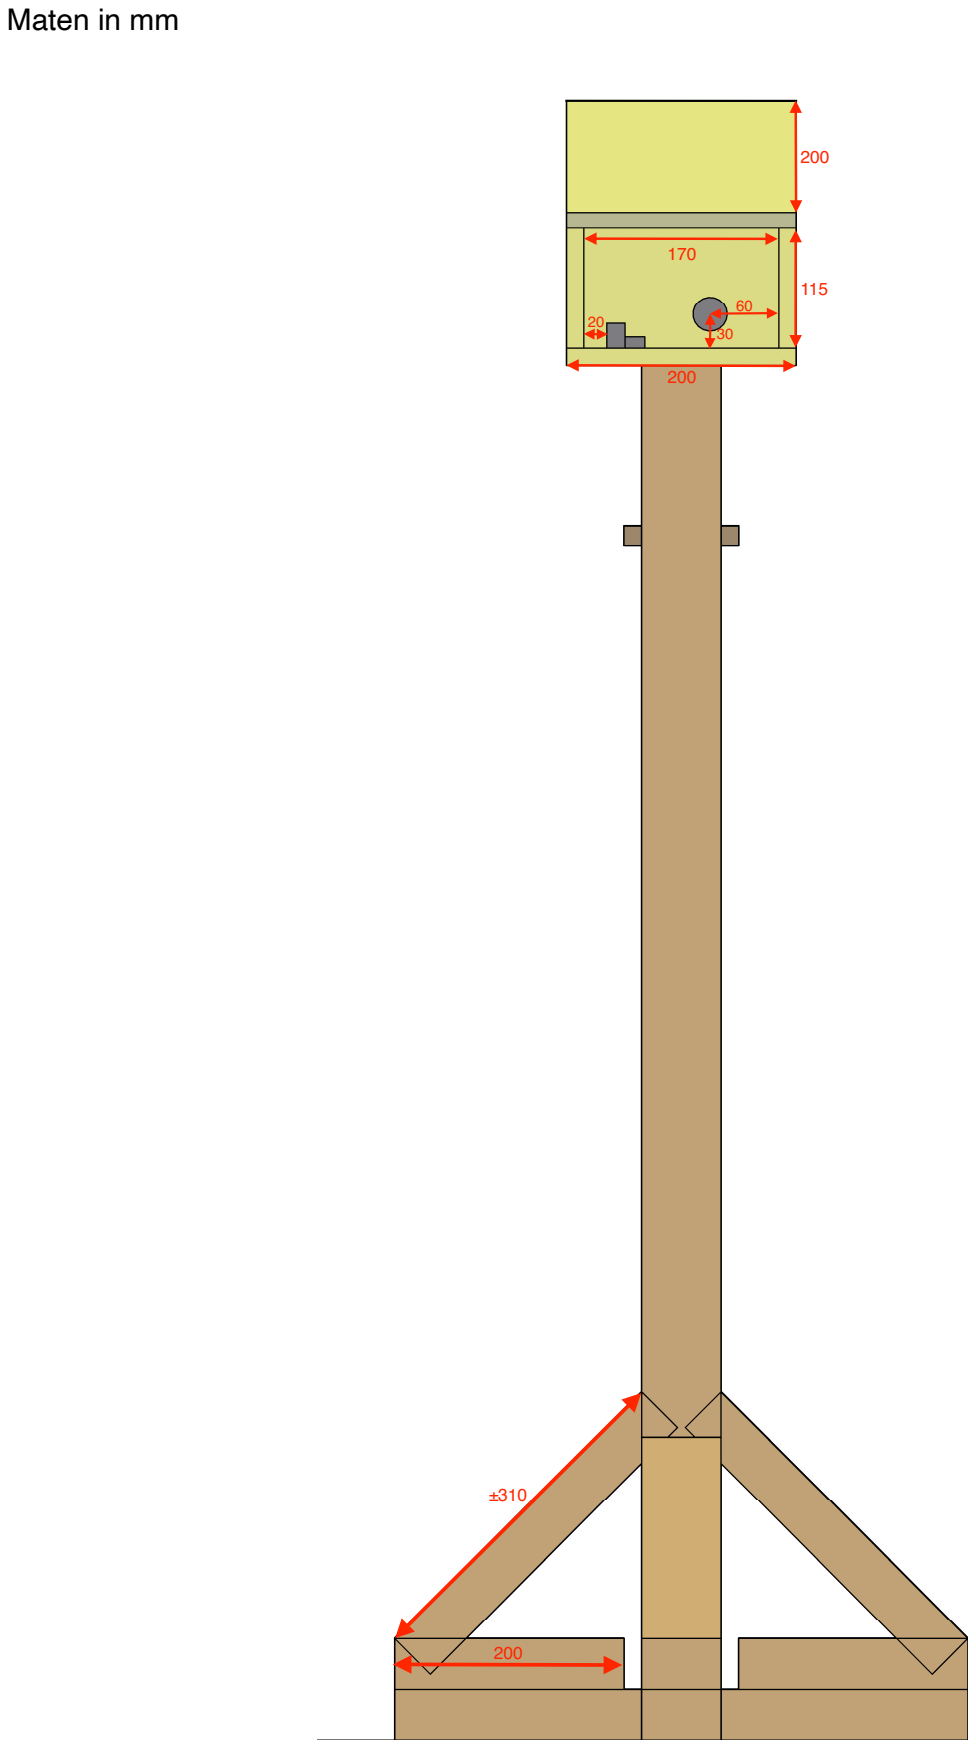
[picture p74: page 1]
