Leandrodn/Project5-6-RDM-RegistatiePaal/Ontwerpen_en_Schema's/3D-Ontwerpen_Afmetingen/Bovenaanzicht-Registratiepaal.pdf

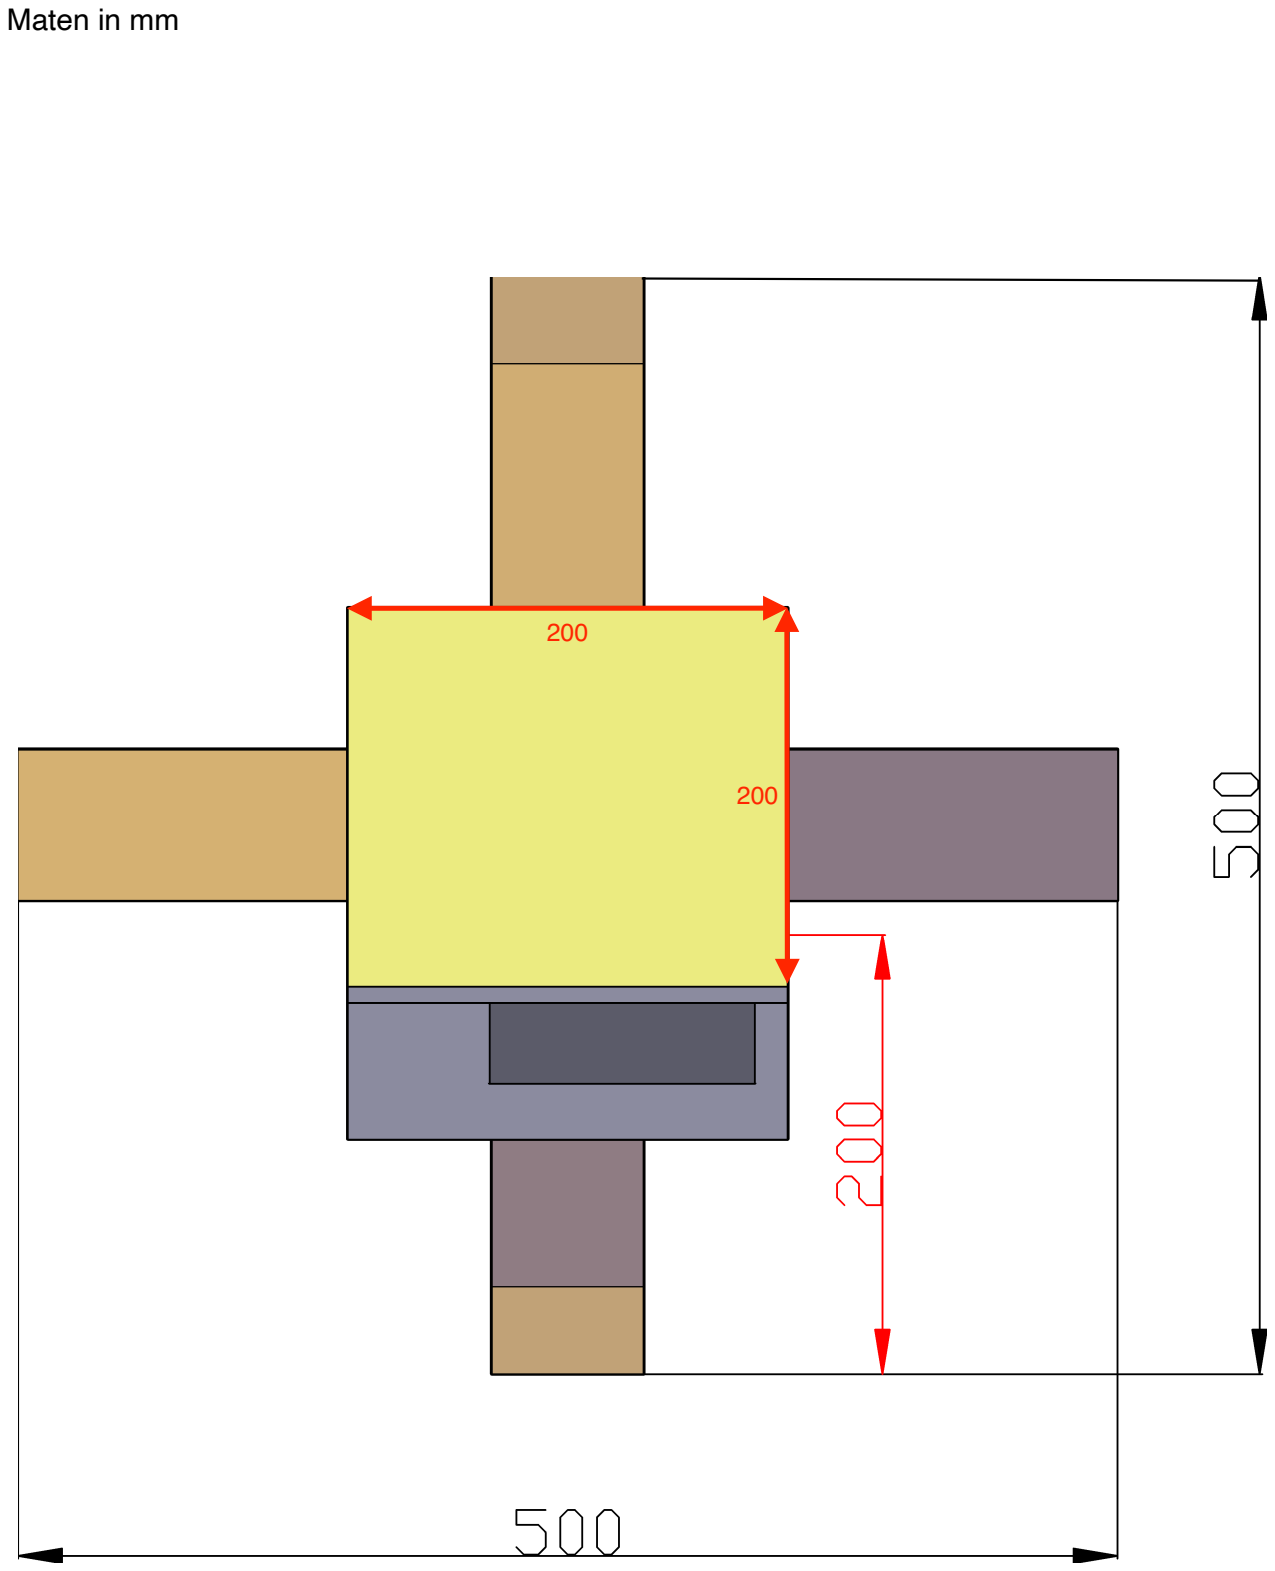
[picture p75: page 1]
