Leandrodn/Project5-6-RDM-RegistatiePaal/Ontwerpen_en_Schema's/3D-Ontwerpen_Afmetingen/Linkeraanzicht-Registratiepaal.pdf

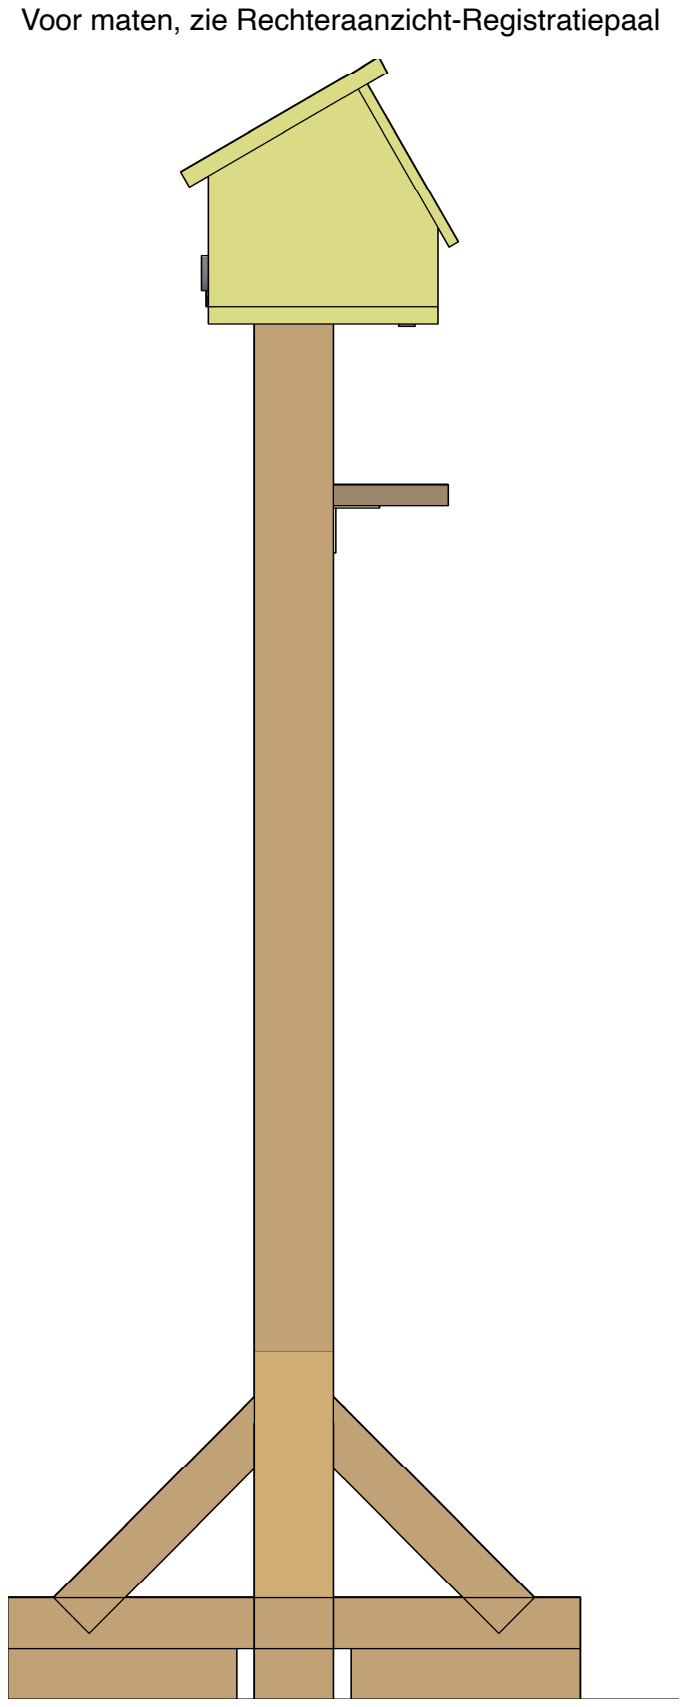
[picture p76: page 1]
