Leandrodn/Project5-6-RDM-RegistatiePaal/Ontwerpen_en_Schema's/3D-Ontwerpen_Afmetingen/Onderaanzicht-Registratiepaal.pdf

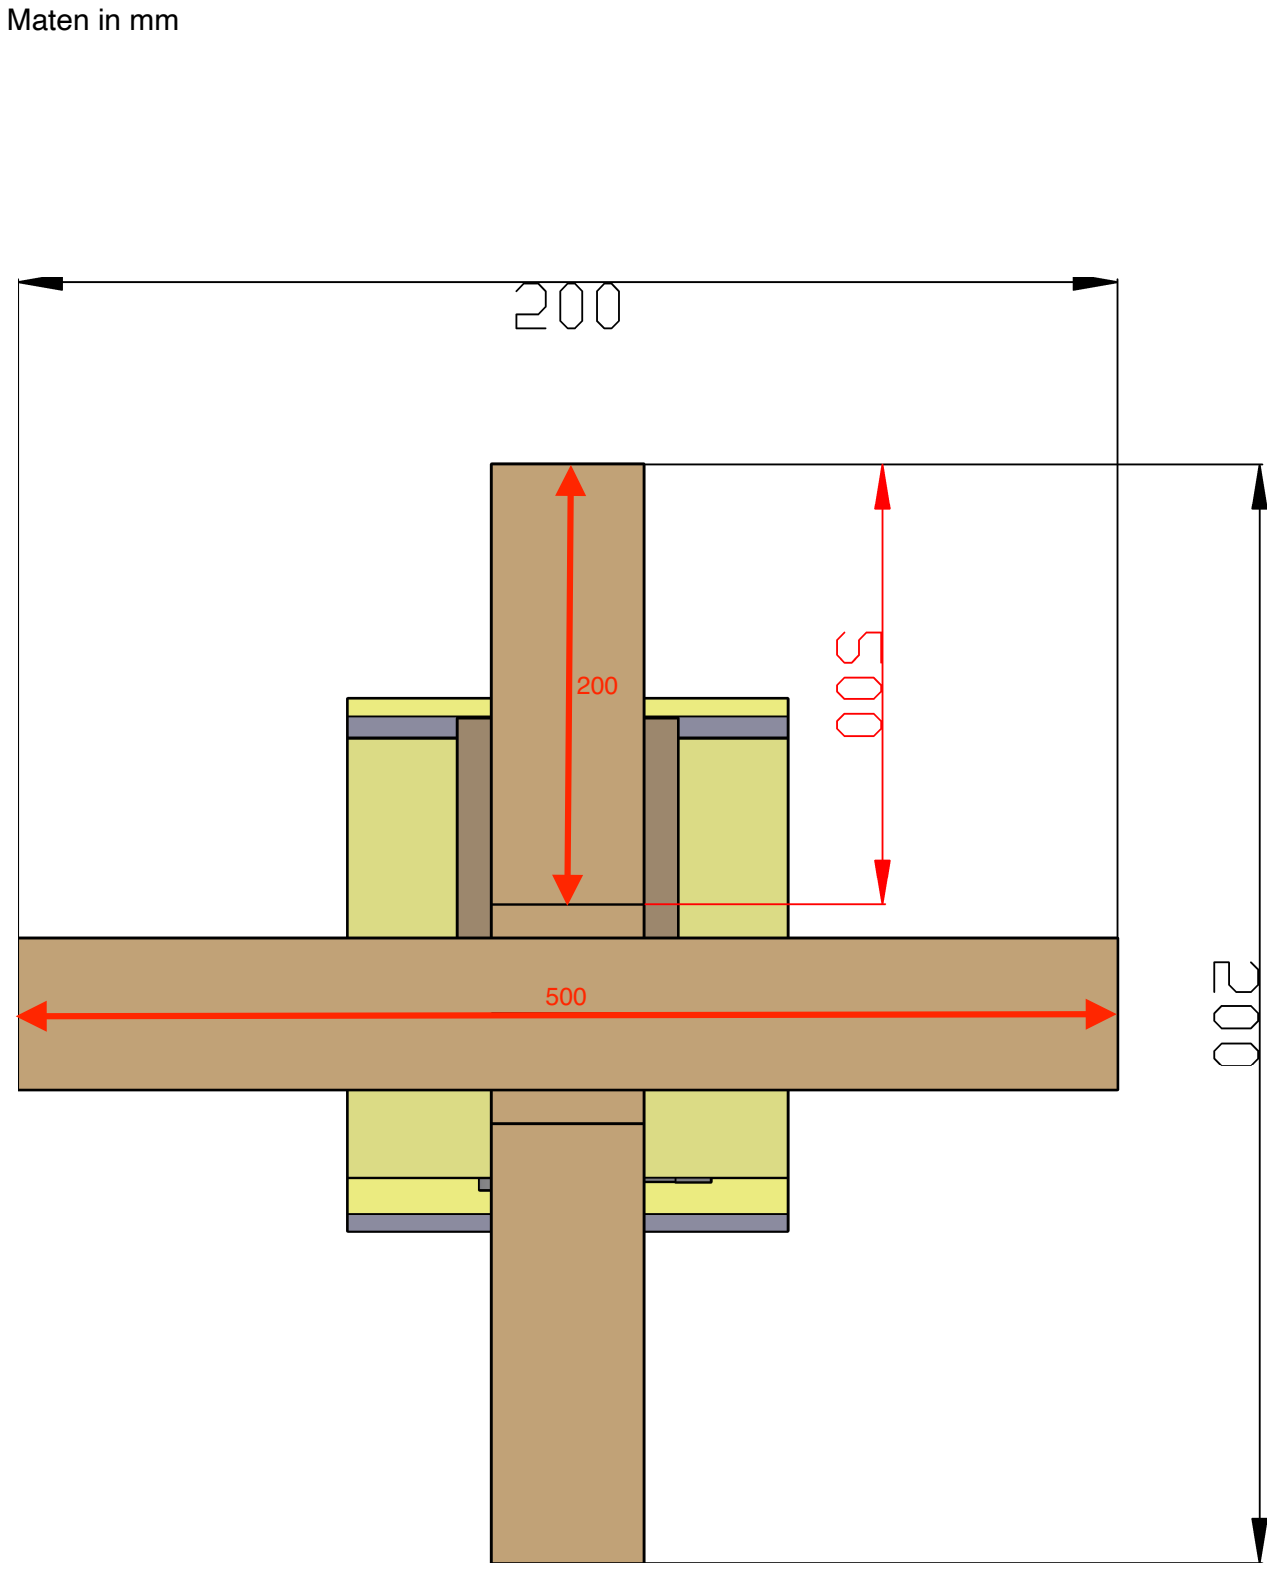
[picture p77: page 1]
