Leandrodn/Project5-6-RDM-RegistatiePaal/Ontwerpen_en_Schema's/3D-Ontwerpen_Afmetingen/Rechteraanzicht-Registratiepaal.pdf

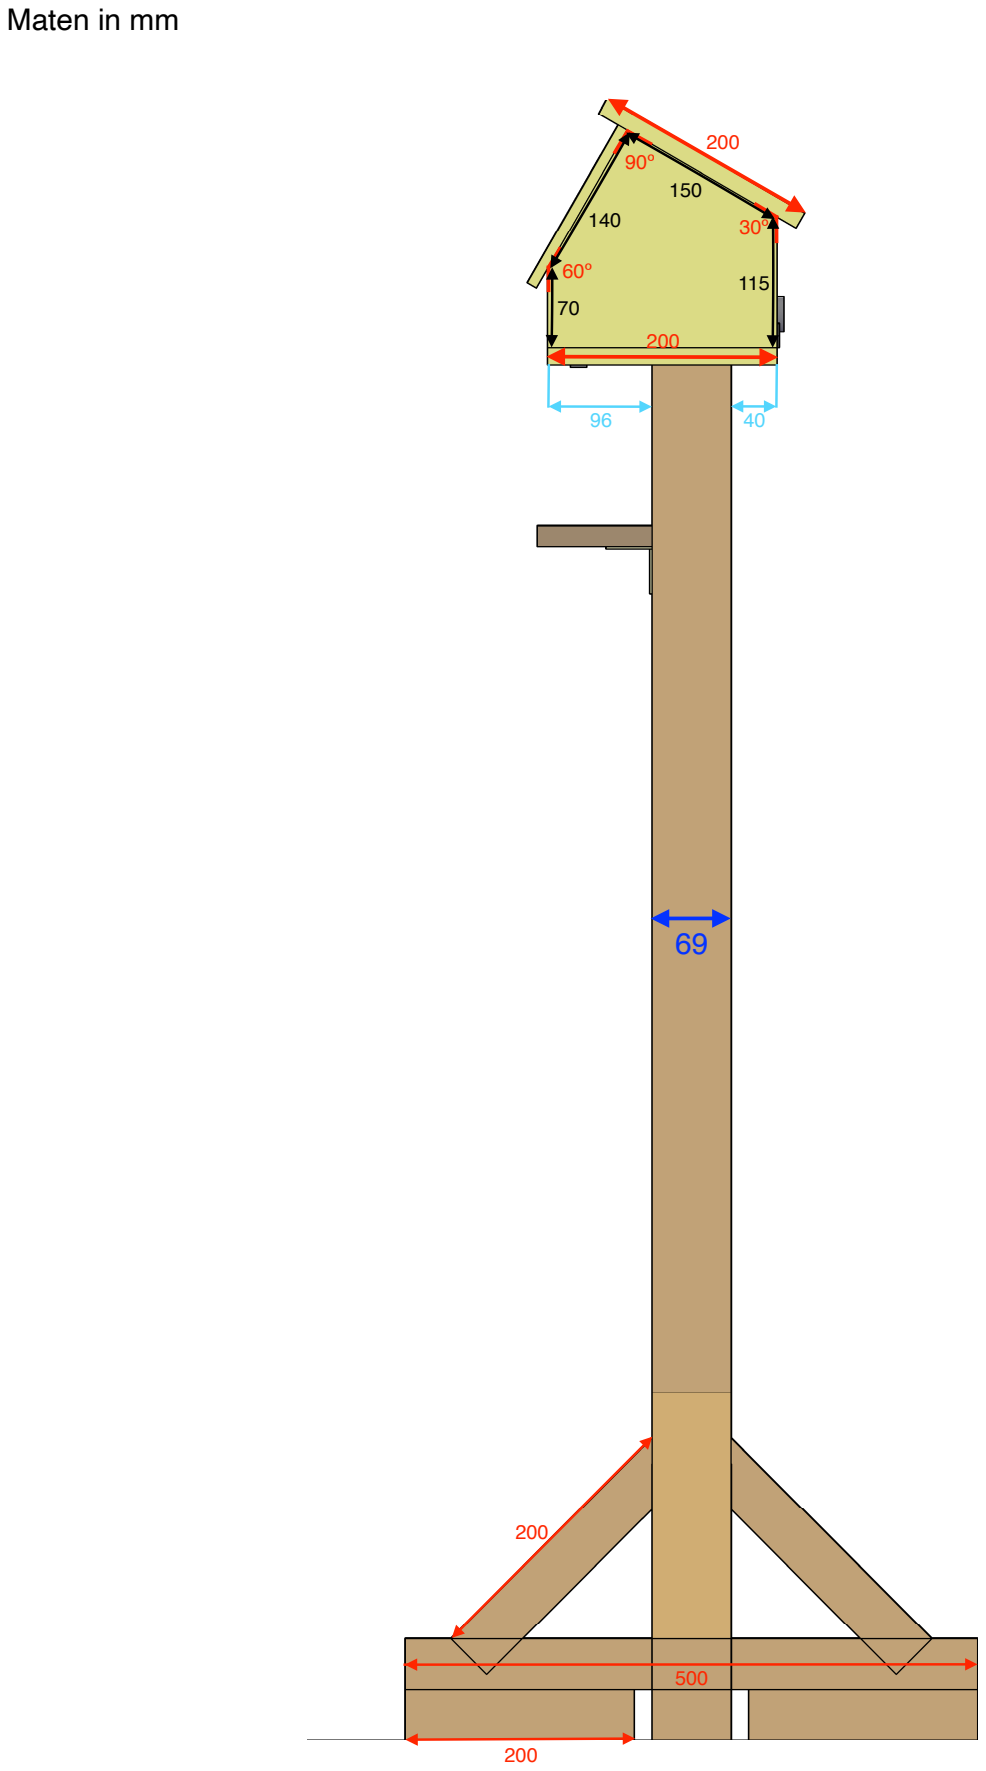
[picture p78: page 1]
