Leandrodn/Project5-6-RDM-RegistatiePaal/Ontwerpen_en_Schema's/3D-Ontwerpen_Afmetingen/Vooraanzicht-Registratiepaal.pdf

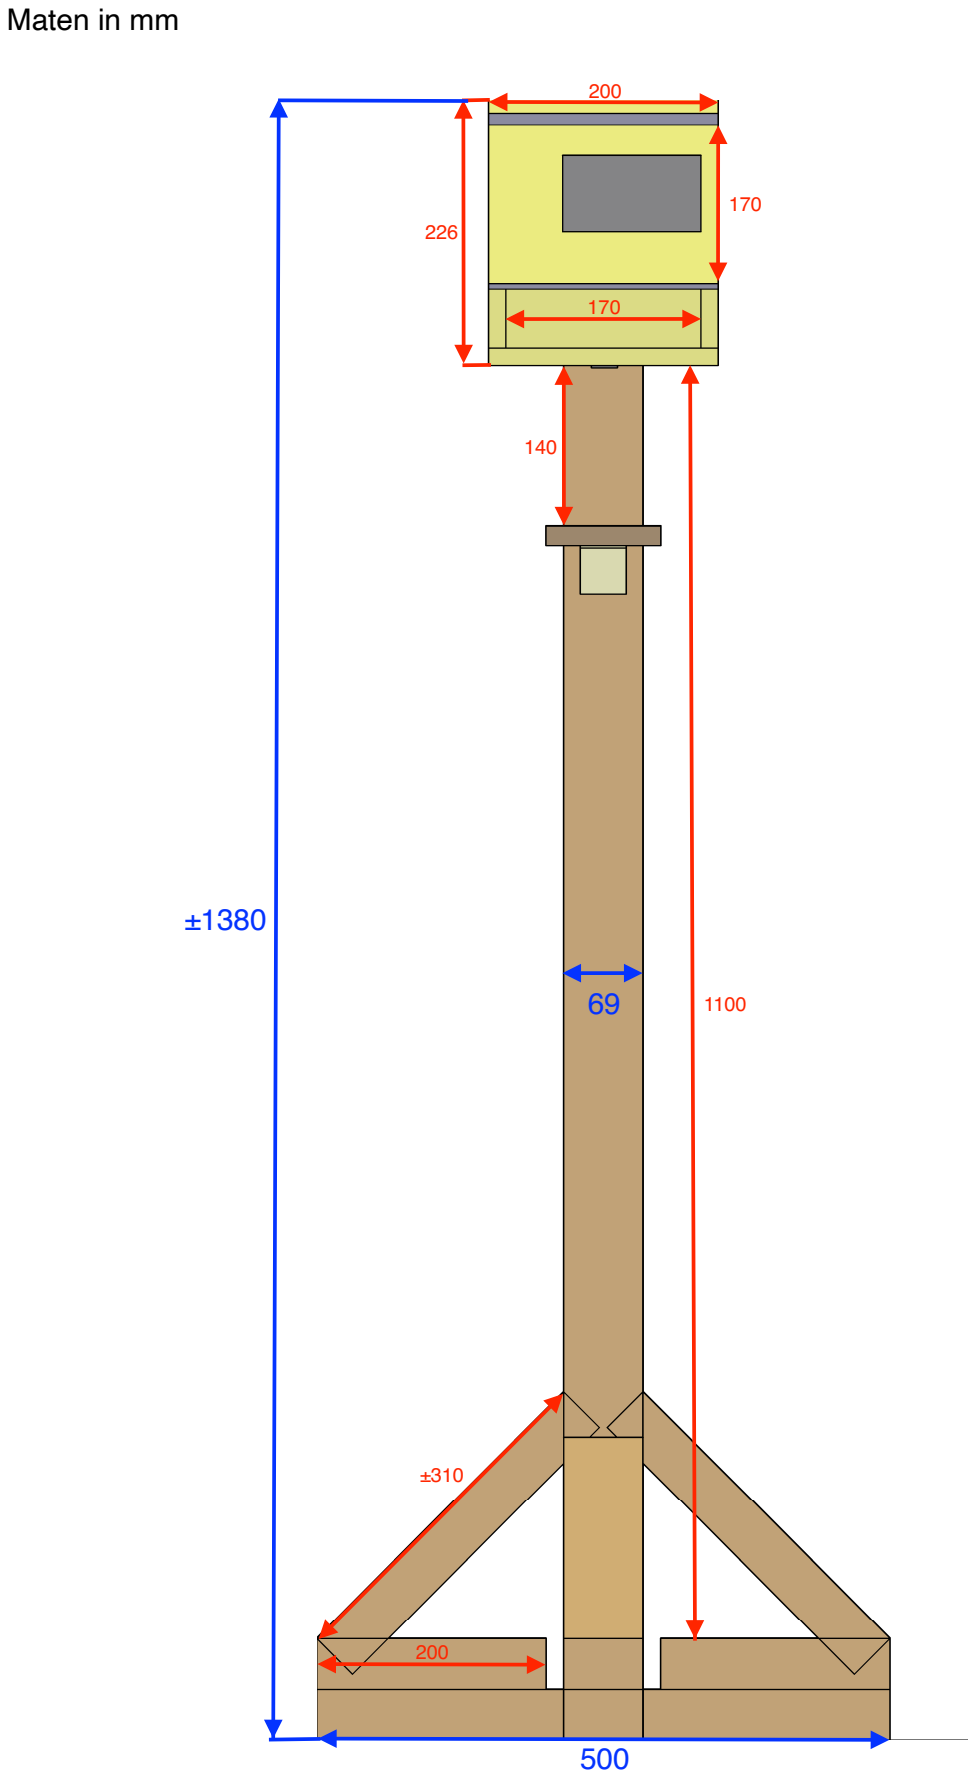
[picture p79: page 1]
