Leandrodn/Project5-6-RDM-RegistatiePaal/Ontwerpen_en_Schema's/Data_Flow_Diagram/Data_Flow_Diagram.pdf

## Server Layer

## Database

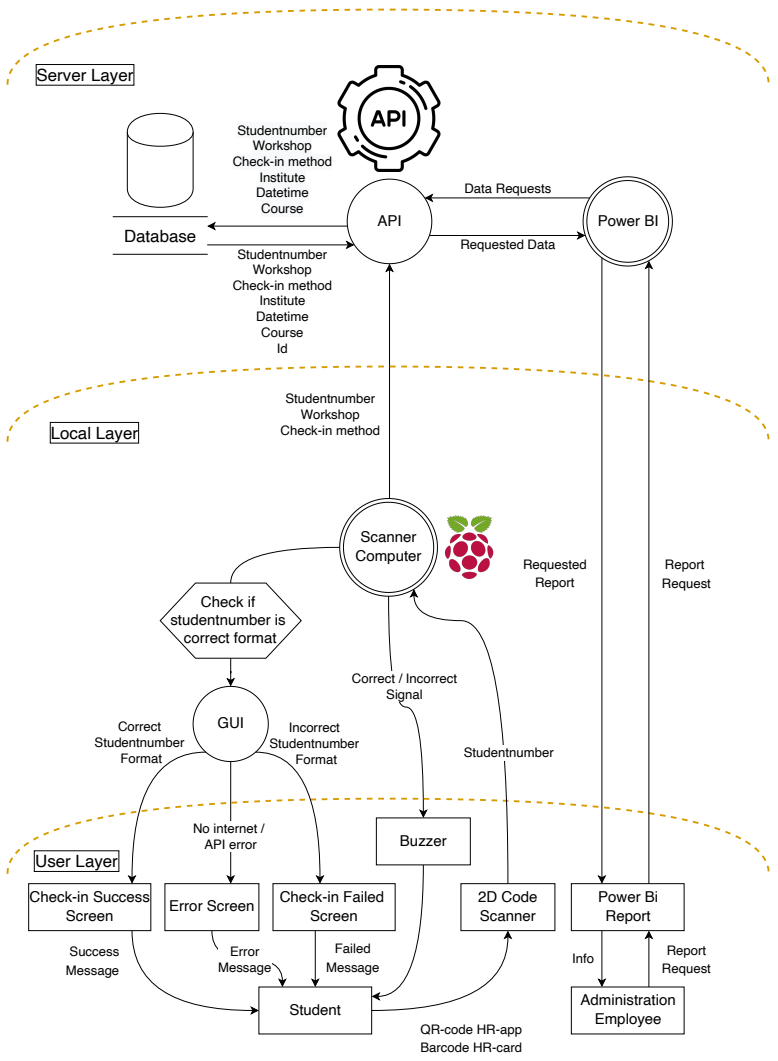
[picture p80: page 1]
Success Message; Correct Studentnumber Format; Correct / Incorrect Signal; Scanner Computer; Local Layer; Studentnumber Workshop Check-in method Institute Datetime Course Id; Studentnumber Workshop Check-in method Institute Datetime Course; Requested Data; API; User Layer; Studentnumber; 2D Code Scanner; Incorrect Studentnumber Format; No internet / API error; GUI; Failed Message; Student; Check if studentnumber is correct format; Requested Report; Data Requests; Power BI; Report Request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

Studentnumber
Workshop
Check-in method

Check-in Success
Screen

Check-in Failed

QR-code HR-app
Barcode HR-card
