Leandrodn/Project5-6-RDM-RegistatiePaal/Ontwerpen_en_Schema's/Flowchart/Flowchart_GUI-MacBookTom.pdf

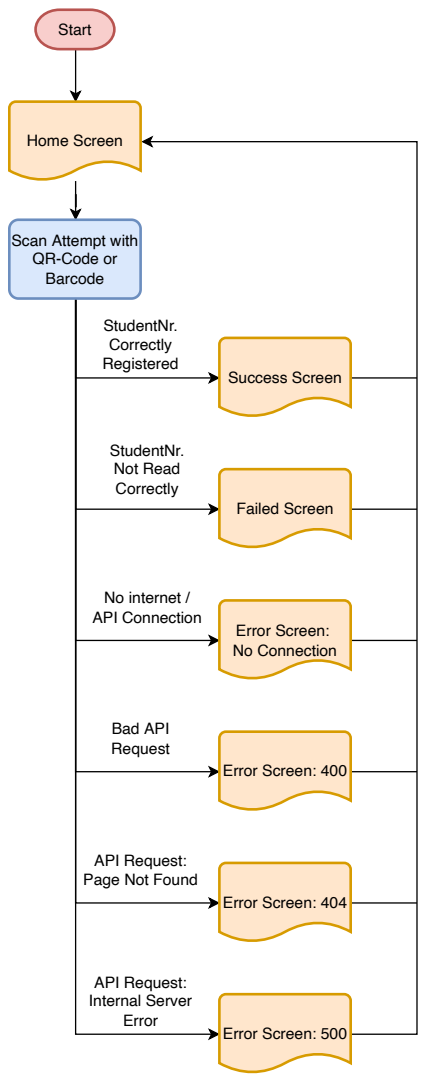
[picture p81: page 1]
Start; Home Screen; Success Screen; Error Screen: No Connection; Failed Screen; Error Screen: 400; Error Screen: 404; Error Screen: 500

Scan Attempt with
QR-Code or
Barcode

StudentNr. Correctly Registered

StudentNr. Not Read Correctly

No internet / API Connection

Bad API Request

API Request: Page Not Found

API Request: Internal Server Error
