Leandrodn/Project5-6-RDM-RegistatiePaal/Ontwerpen_en_Schema's/Flowchart/Flowchart_GUI.pdf

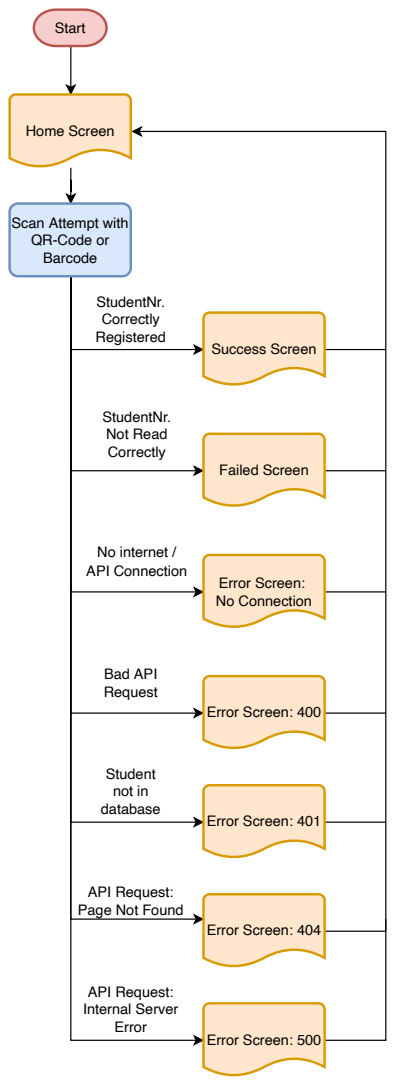
[picture p82: page 1]
Start; Home Screen; Success Screen; Error Screen: No Connection; Failed Screen; Error Screen: 400; Error Screen: 404; Error Screen: 500; Error Screen: 401

Scan Attempt with
QR-Code or
Barcode

StudentNr. Correctly Registered

StudentNr. Not Read Correctly

No internet / API Connection

Bad API Request

Student not in database

API Request: Page Not Found

API Request: Internal Server Error
