Leandrodn/Project5-6-RDM-RegistatiePaal/Ontwerpen_en_Schema's/Software_Diagram/SoftwareDiagram-MacBookTom.pdf

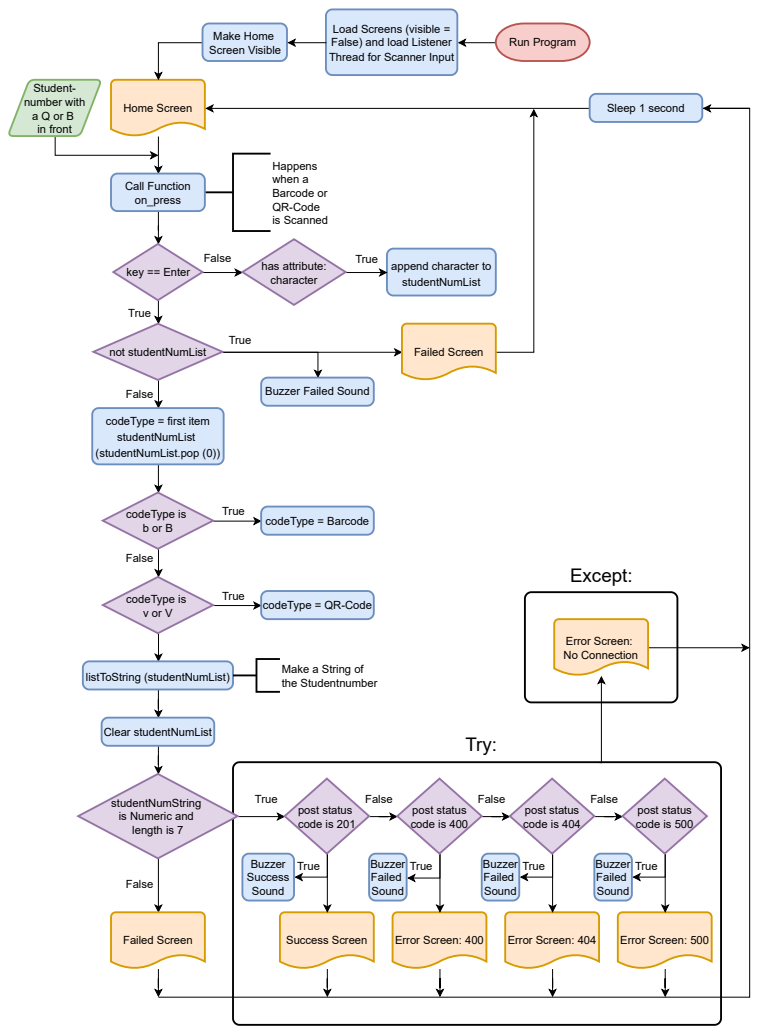
[picture p83: page 1]
Run Program; Home Screen; Success Screen; Error Screen: No Connection; Error Screen: 400; Error Screen: 404; Error Screen: 500; Student- number with a Q or B in front; Happens when a Barcode or QR-Code is Scanned; Call Function on_press; True; False; key == Enter; not studentNumList; Failed Screen; codeType is; codeType = Barcode; codeType = QR-Code; listToString (studentNumList); Clear studentNumList; post status code is 201; post status code is 400; post status code is 404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

Load Screens (visible =
False) and load Listener
Thread for Scanner Input

True has attribute:
character

append character to
studentNumList

Buzzer Failed Sound

codeType = first item
(studentNumList.pop (0))

Make a String of
the Studentnumber

True studentNumString
is Numeric and
length is 7
