Leandrodn/Project5-6-RDM-RegistatiePaal/Onderzoek/Experimenteel_Onderzoek/Test_Code/Overige_Test_Code/RPi_buzzer_and_LED.py

#Libraries
from gpiozero import Buzzer, LED
from time import sleep

#Set buzzer
buzzer = Buzzer (12)

#Set LED
led = LED(14)

#make variable timeOn and timeOff
timeOn = 0.5
timeOff = 2

timeX = 0.2

def buzz ():
    buzzer.value = 1
    sleep (timeX)
    buzzer.value = 0
    sleep (timeX)
    buzzer.value = 1
    sleep (timeX)
    buzzer.value = 0
    sleep (timeX)
    buzzer.value = 1
    sleep (timeX)
    buzzer.value = 0 
    
#Forever loop:
try:
    '''while True:
        buzzer.toggle ()
        led.toggle ()
        sleep (timeOn)
        buzzer.toggle ()
        led.toggle ()
        sleep (timeOff)
        '''
    buzz ()
except KeyboardInterrupt:
    print ('exiting...')
